bengineer91/Preamp/layout/back.PNG

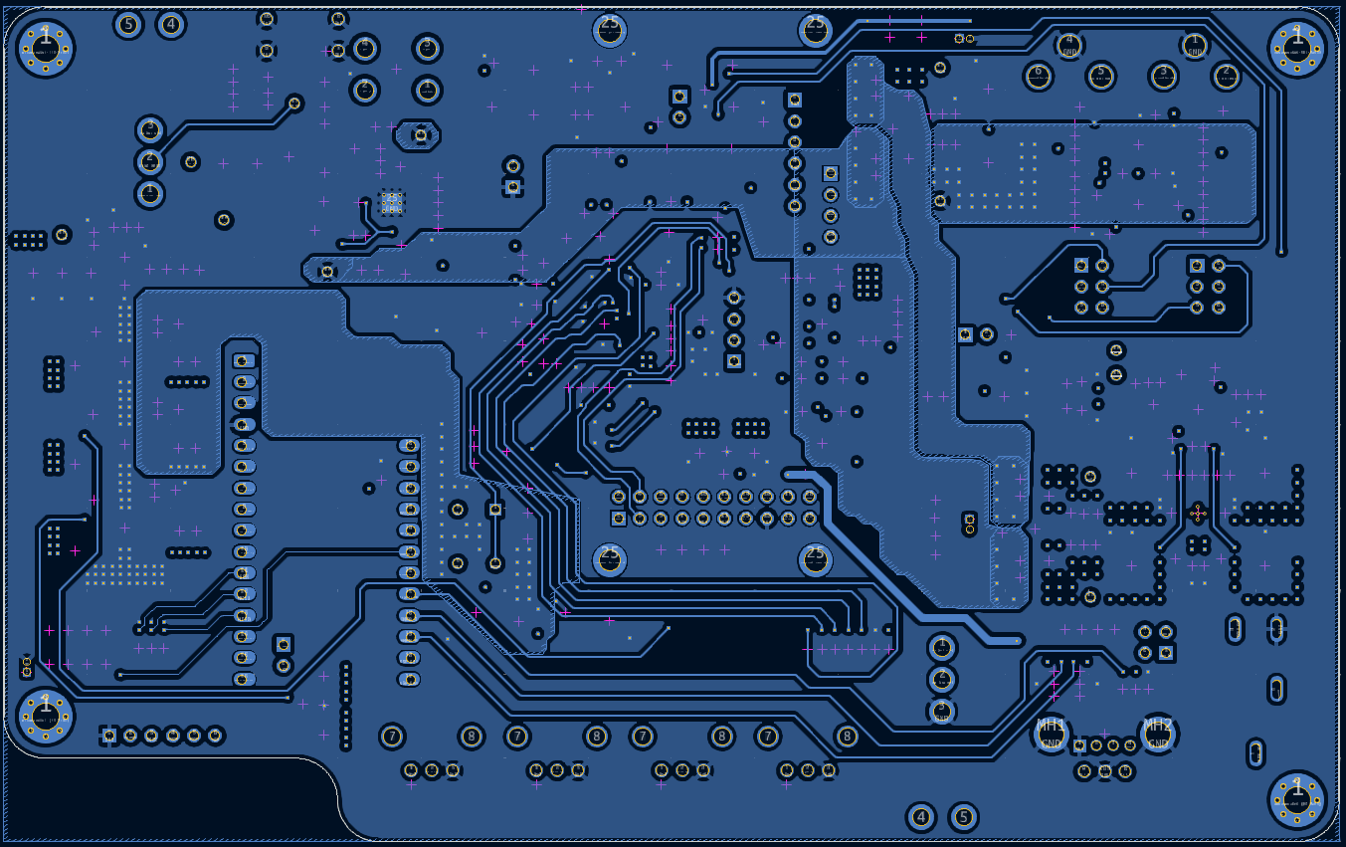
layout/back.PNG
