bengineer91/Preamp/layout/front.PNG

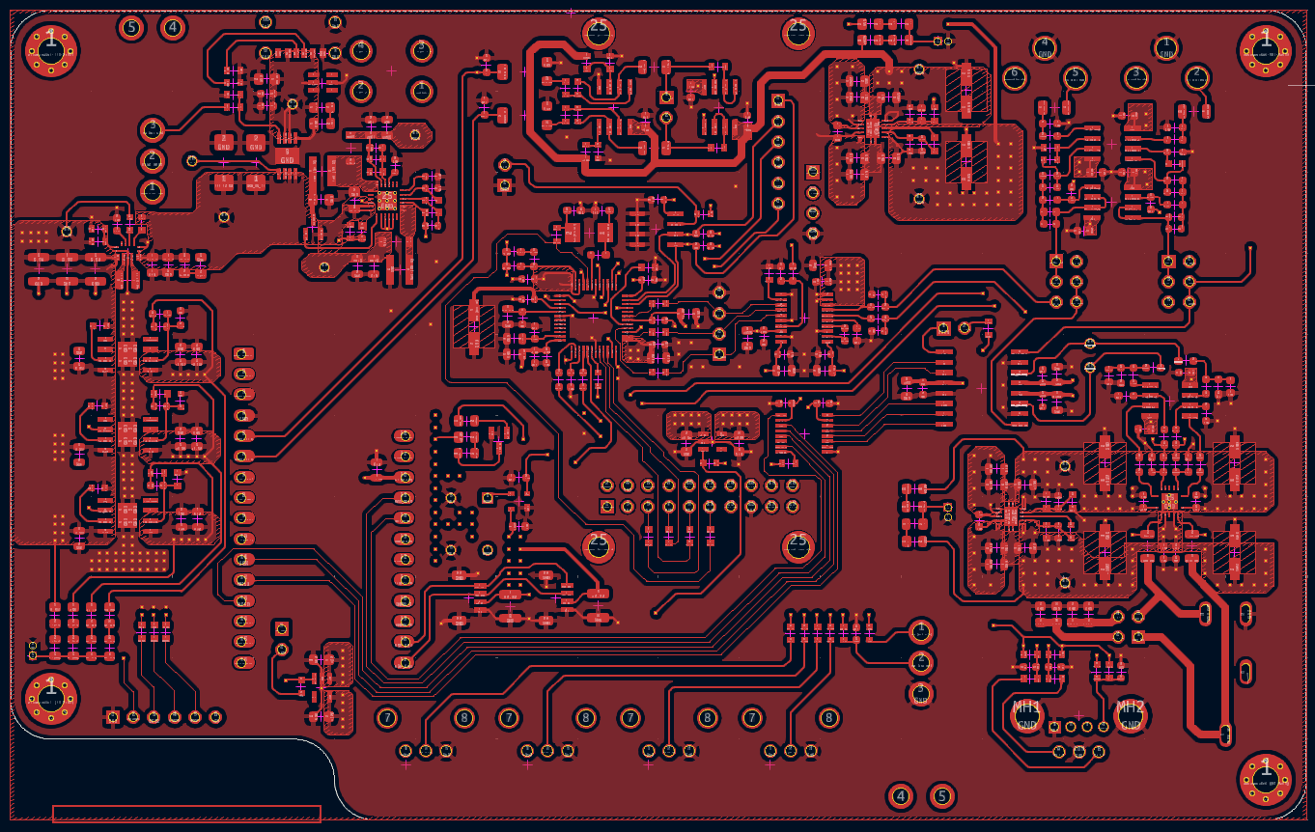
layout/front.PNG
