bengineer91/Preamp/layout/front_w_silk.PNG

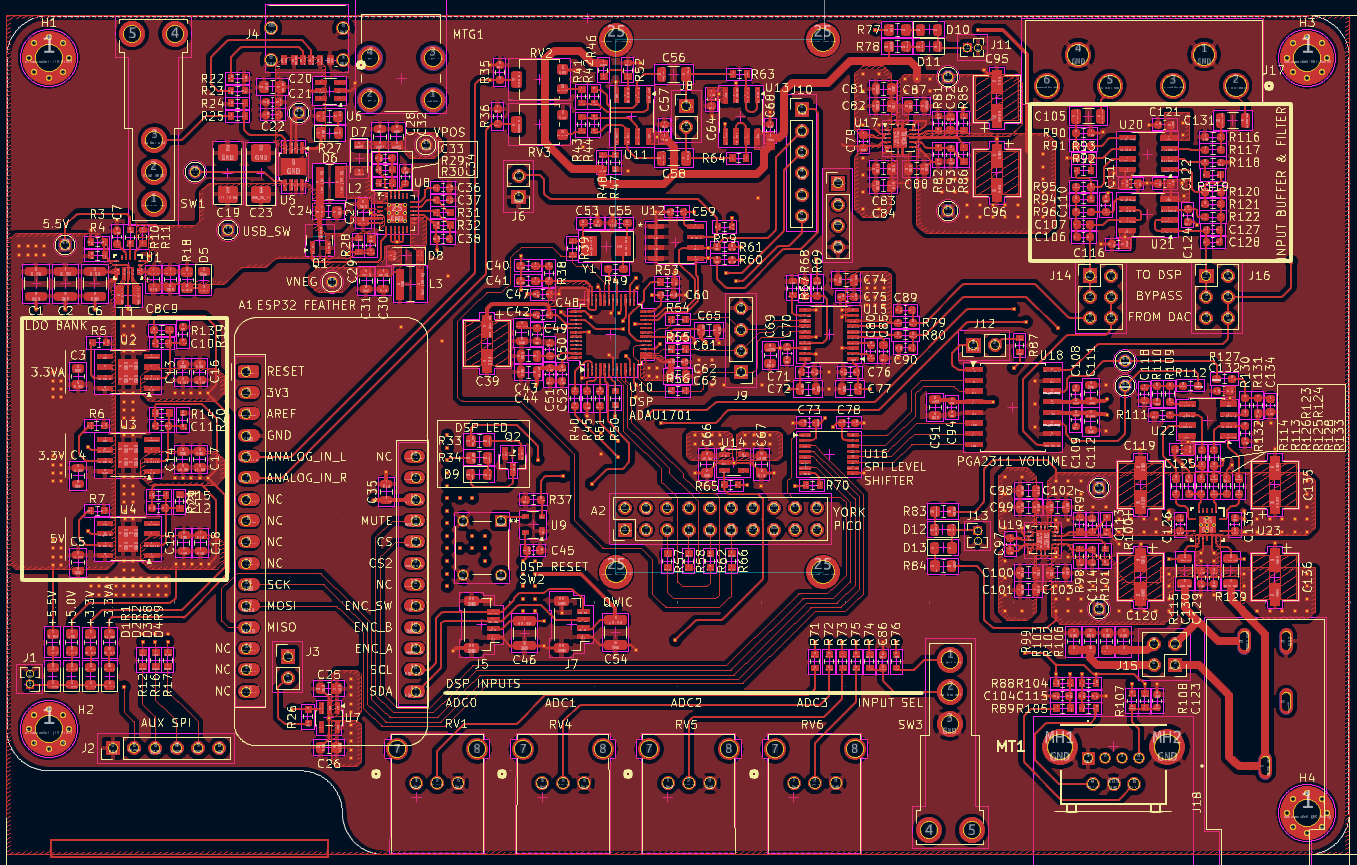
layout/front_w_silk.PNG
