bengineer91/Preamp/layout/in1_gnd.PNG

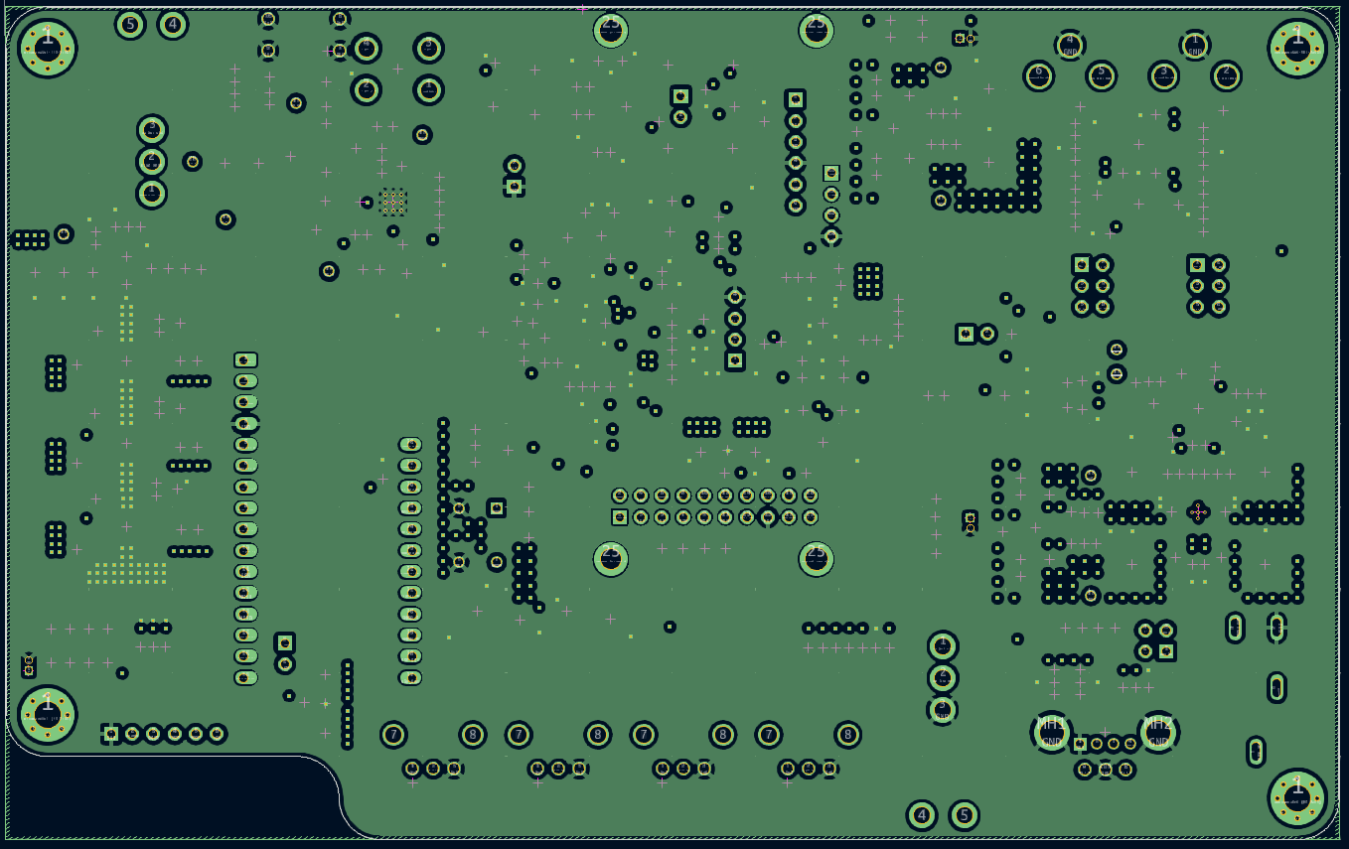
layout/in1_gnd.PNG
