bengineer91/Preamp/layout/in2_pwr.PNG

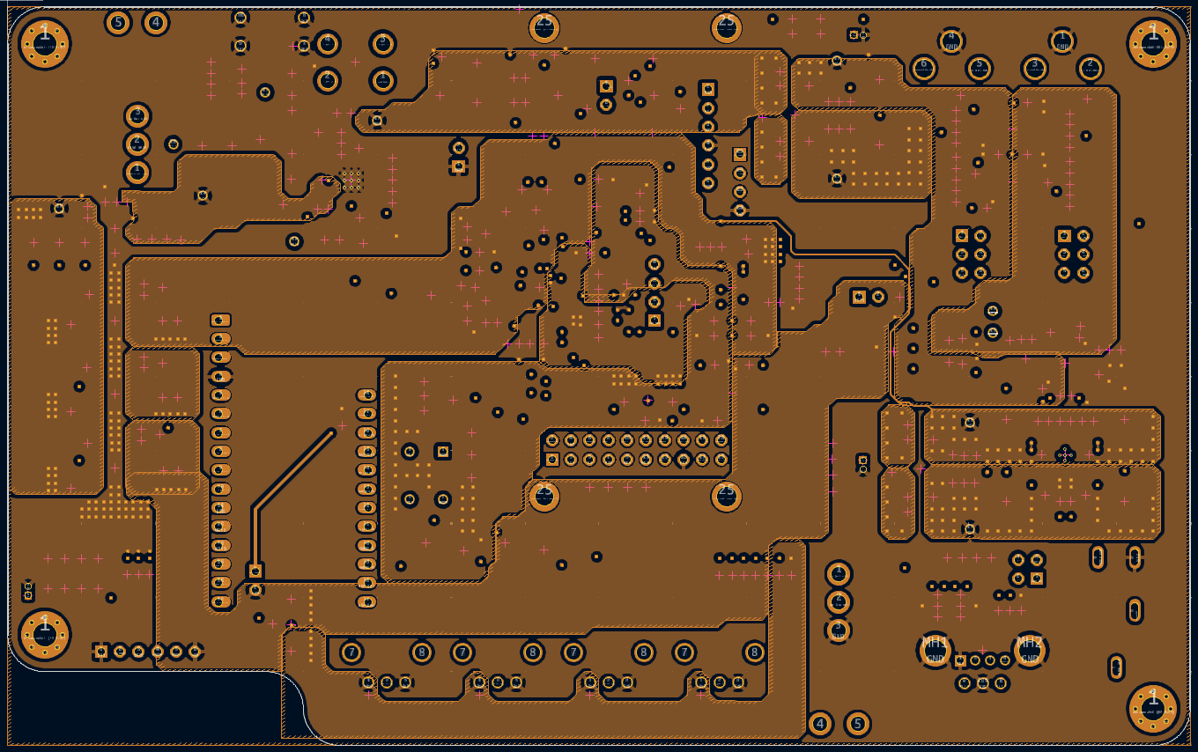
layout/in2_pwr.PNG
