bengineer91/Preamp/schematic/sheet2.png

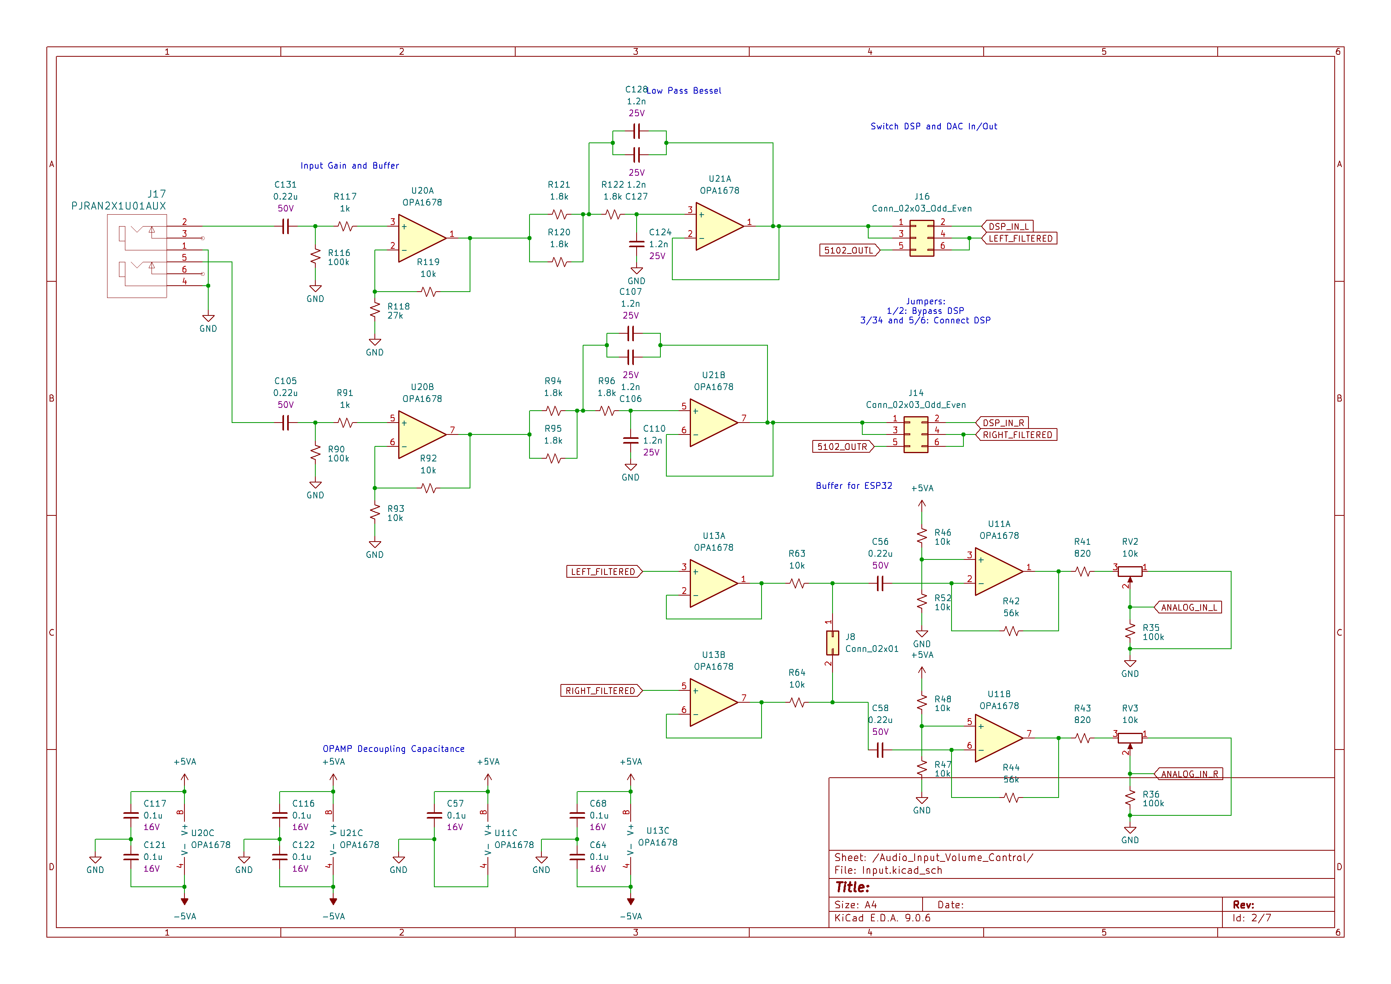
schematic/sheet2.png
