bengineer91/Preamp/schematic/sheet6.png

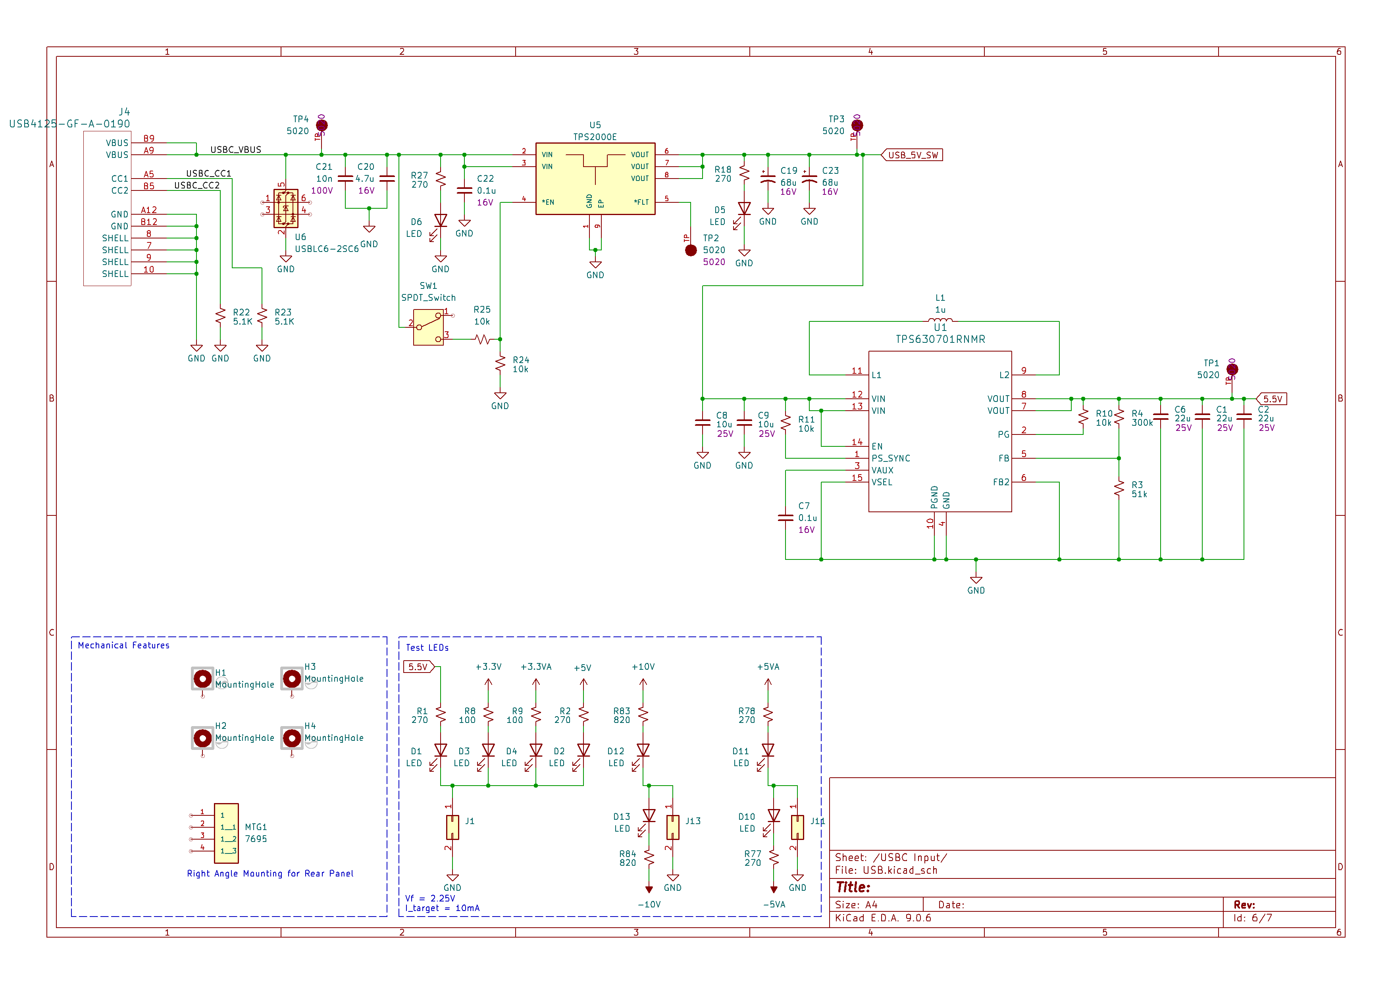
schematic/sheet6.png
