bengineer91/Preamp/schematic/sheet7.png

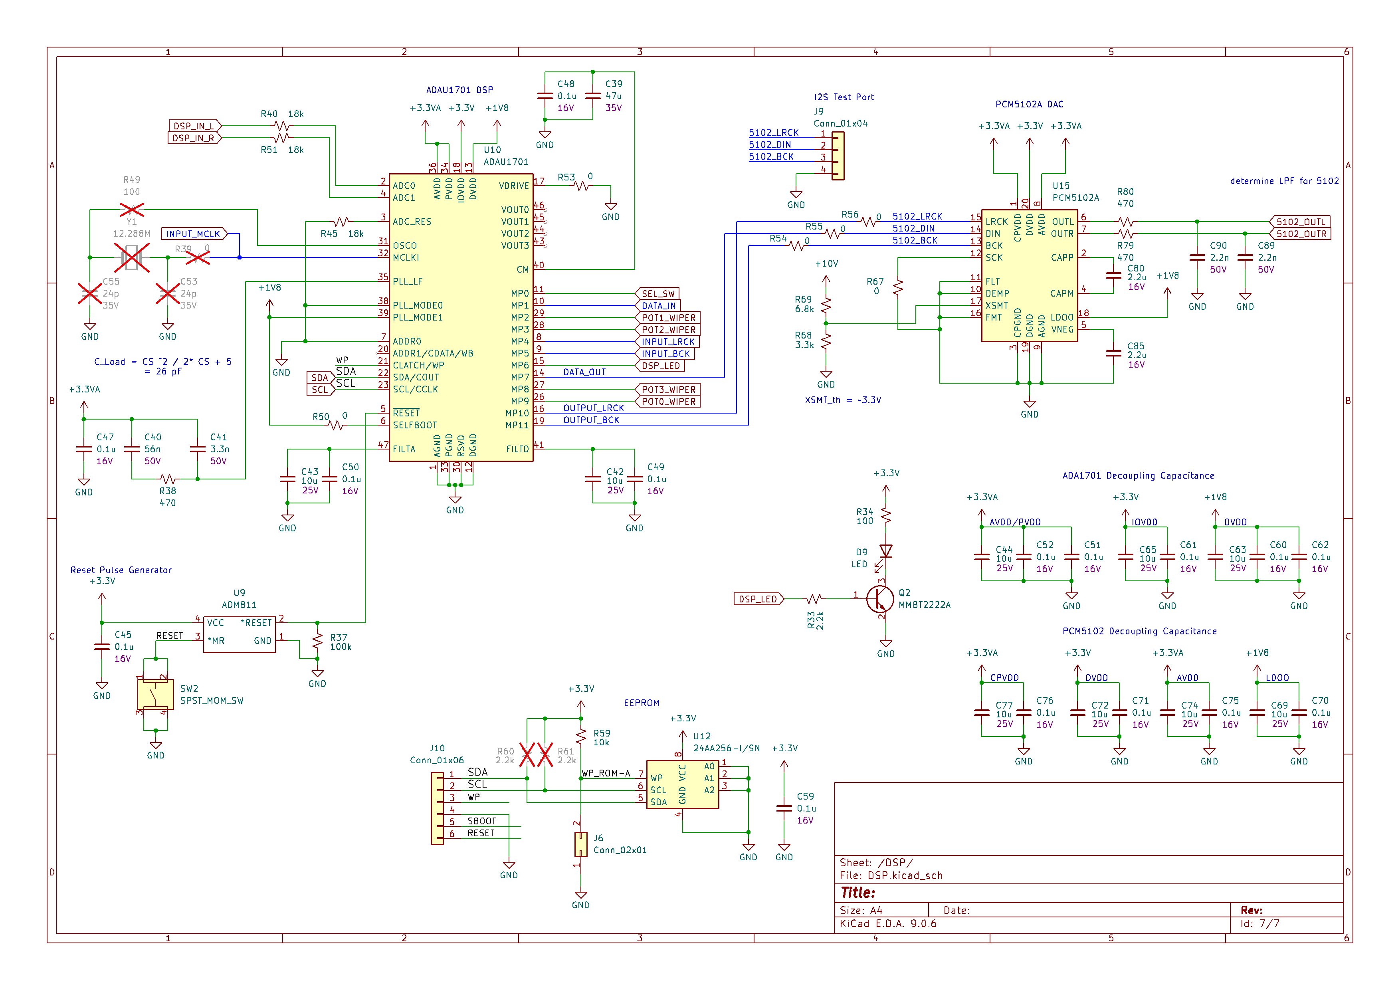
schematic/sheet7.png
