bengineer91/Preamp/kicad/DSP.kicad_sch

## KiCad design kicad/DSP.kicad_sch (2026-02-03)

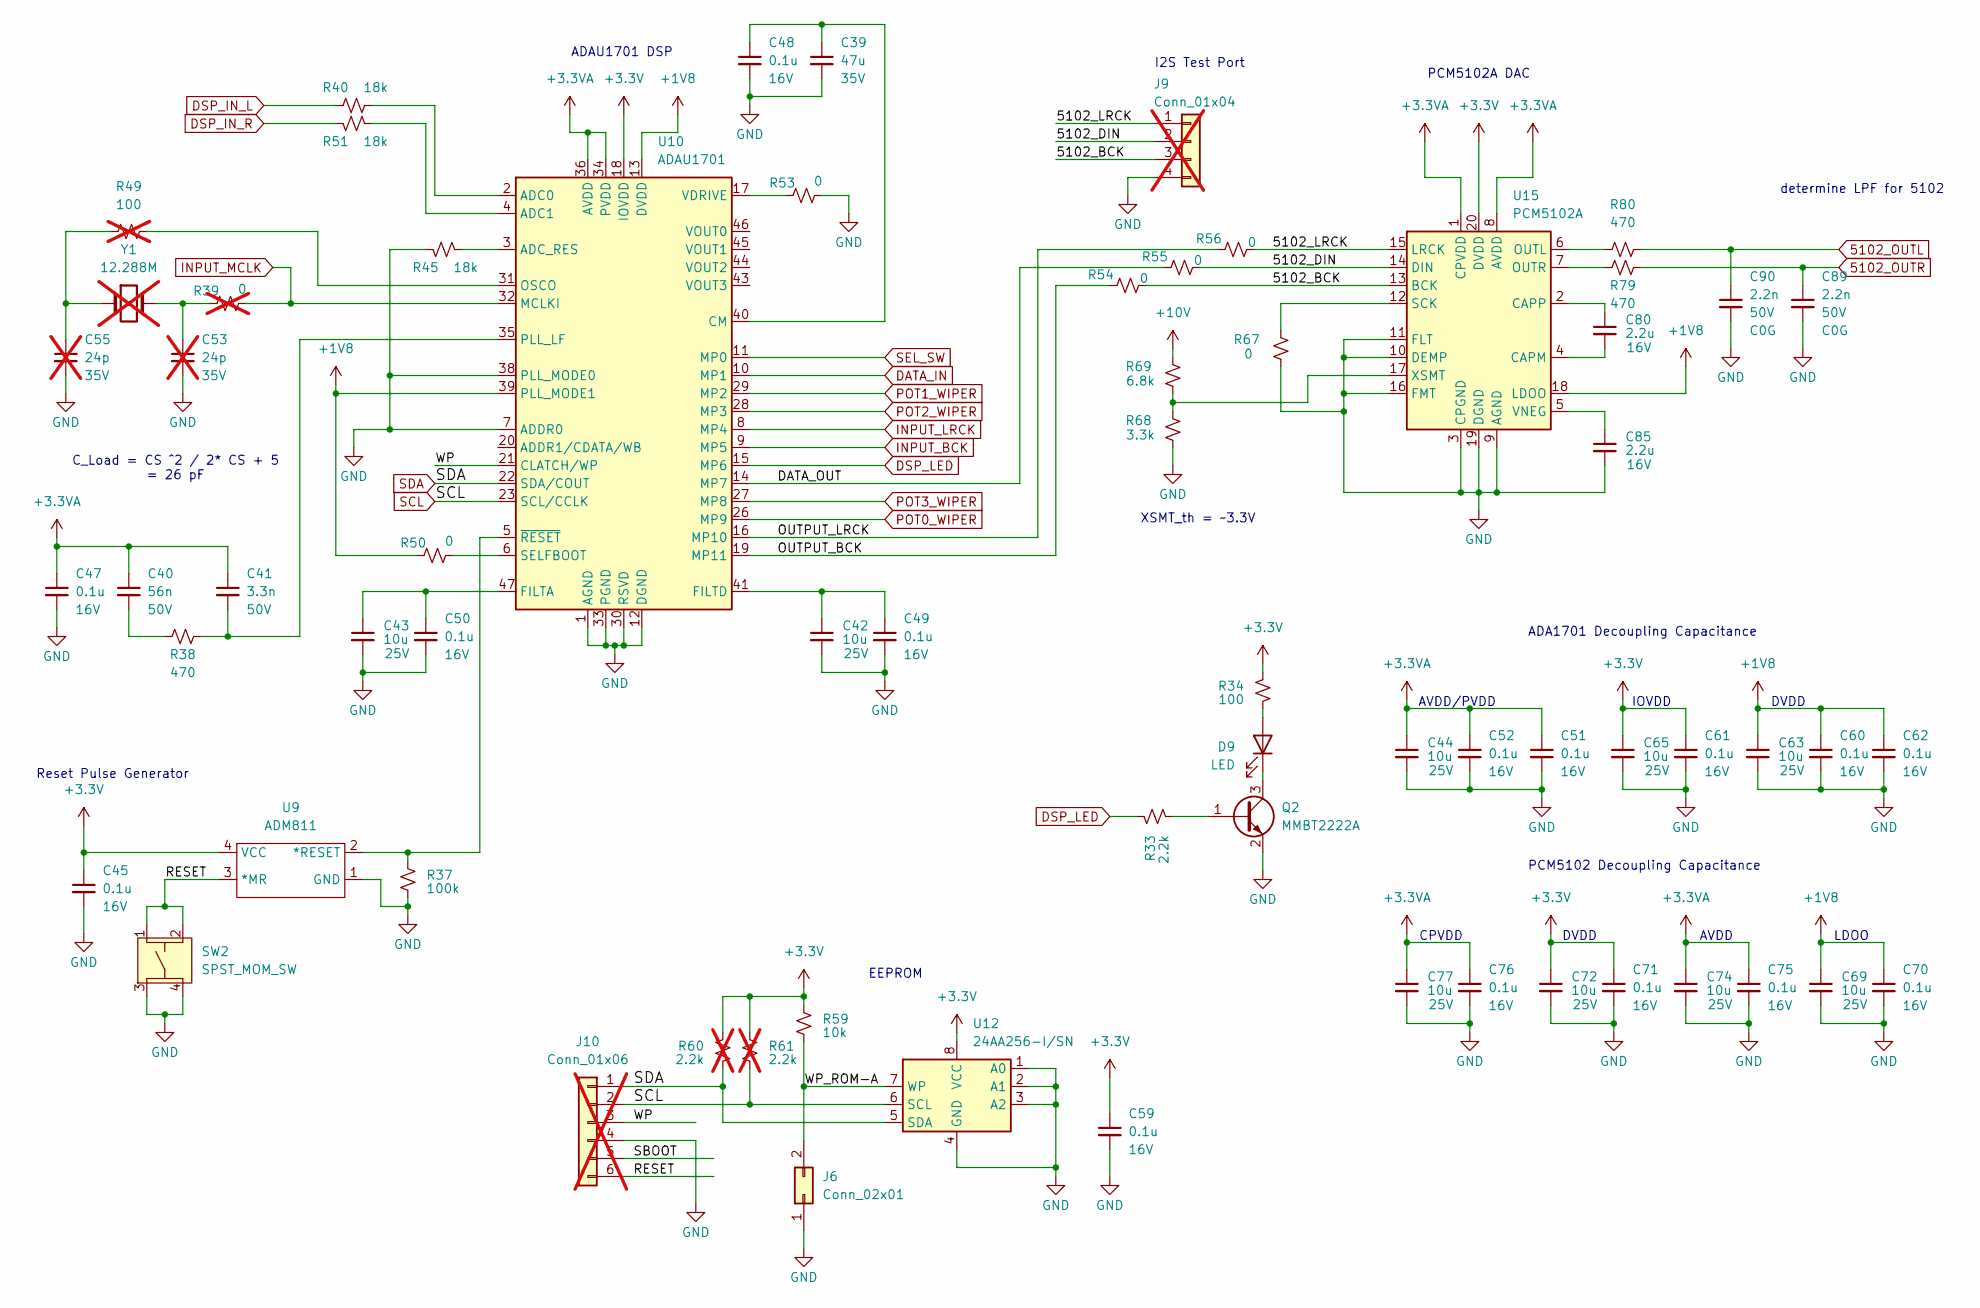
[picture p24: schematic DSP.kicad_sch]

Parts:
C39: 47u; CAP_UCD_5X5P8_NCH; Voltage 35V; Part Number UCM1V470MCL1GS
C40: 56n; C_0603_1608Metric_Pad1.08x0.95mm_HandSolder; Voltage 50V; Part Number GCM188R71H563KA57D
C41: 3.3n; C_0603_1608Metric_Pad1.08x0.95mm_HandSolder; Voltage 50V; Part Number GRM1885C1H332JA01D
C42, C43, C44, C63, C65, C69, C72, C74, C77: 10u; C_0805_2012Metric; Voltage 25V; Part Number GRM21BZ71E106KE15L
C45, C47, C48, C49, C50, C51, C52, C59, C60, C61, C62, C70, C71, C75, C76: 0.1u; C_0603_1608Metric; Voltage 16V; Part Number GCJ188R71C104KA01D
C53, C55: 24p; C_0603_1608Metric_Pad1.08x0.95mm_HandSolder; Voltage 35V; not fitted
C80, C85: 2.2u; C_0603_1608Metric; Voltage 16V; Part Number GRM188Z71E225ME43D
C89, C90: 2.2n; C_0603_1608Metric; Voltage 50V; Part Number GRM1885C1H222JA01D
D9: LED; LED_0805_2012Metric_Pad1.15x1.40mm_HandSolder; Part Number APT2012PGW
J6: Conn_02x01; PinHeader_1x02_P2.54mm_Vertical
J9: Conn_01x04; PinHeader_1x04_P2.54mm_Vertical; not fitted
J10: Conn_01x06; PinHeader_1x06_P2.54mm_Vertical; not fitted
Q2: MMBT2222A; SOT-23; Part Number MMBT2222A
R33: 2.2k; R_0805_2012Metric_Pad1.20x1.40mm_HandSolder; Part Number CRCW08052K20FKEA
R34: 100; R_0805_2012Metric_HandSolder; Part Number CRCW0805150RFKEA
R37: 100k; R_0603_1608Metric; Part Number CRCW0603100KFKEA
R38, R79, R80: 470; R_0603_1608Metric; Part Number CRCW0603470RFKEA
R39: 0; R_0603_1608Metric; Part Number CRCW06030000Z0EA; not fitted
R40, R45, R51: 18k; R_0603_1608Metric; Part Number CRCW060318K0FKEA
R49: 100; R_0603_1608Metric_Pad0.98x0.95mm_HandSolder; Part Number CRCW0805100RFKEA; not fitted
R50, R53, R54, R55, R56, R67: 0; R_0603_1608Metric; Part Number CRCW06030000Z0EA
R59: 10k; R_0603_1608Metric; Part Number CRCW060310K0FKEA
R60, R61: 2.2k; R_0603_1608Metric_Pad0.98x0.95mm_HandSolder; Part Number CRCW06032K20FKEA; not fitted
R68: 3.3k; R_0603_1608Metric_Pad0.98x0.95mm_HandSolder
R69: 6.8k; R_0603_1608Metric
SW2: SPST_MOM_SW; SW4_1825910-B_TEC
U9: ADM811; SOT-143; Part Number ADM811-3TARTZ-RL7
U10: ADAU1701; LQFP-48_7x7mm_P0.5mm; Manufacturer_Part_Number ADAU1701JSTZ-RL
U12: 24AA256-I/SN; SOIC8-N_MC_MCH; Part Number 24AA256-I/SN
U15: PCM5102A; TSSOP-20_4.4x6.5mm_P0.65mm; Manufacturer_Part_Number PCM5102APWR
Y1: 12.288M; Crystal_SMD_Abracon_ABM3-2Pin_5.0x3.2mm; not fitted

Connections:
5102_BCK: J9.3, R54.2, U15.13 (BCK)
5102_DIN: J9.2, R55.2, U15.14 (DIN)
5102_LRCK: J9.1, R56.2, U15.15 (LRCK)
5102_OUTL: C90.1, R80.2
5102_OUTR: C89.1, R79.2
+1V8: C60.1, C62.1, C63.1, C69.1, C70.1, R50.1, U10.13 (DVDD), U10.24 (DVDD), U10.39 (PLL_MODE1), U15.18 (LDOO)
+3.3V: C45.1, C59.1, C61.1, C65.1, C71.1, C72.1, R34.1, R59.1, R60.1, R61.1, U9.4 (VCC), U10.18 (IOVDD), U12.8 (VCC), U15.20 (DVDD)
+3.3VA: C40.1, C41.1, C44.1, C47.1, C51.1, C52.1, C74.1, C75.1, C76.1, C77.1, U10.34 (PVDD), U10.36 (AVDD), U10.48 (AVDD), U15.1 (CPVDD), U15.8 (AVDD)
+10V: R69.2
DATA_IN: U10.10 (MP1)
DATA_OUT: R55.1, U10.14 (MP7)
DSP_IN_L: R40.1
DSP_IN_R: R51.1
DSP_LED: R33.1, U10.15 (MP6)
GND: C39.2, C42.2, C43.2, C44.2, C45.2, C47.2, C48.2, C49.2, C50.2, C51.2, C52.2, C53.2, C55.2, C59.2, C60.2, C61.2, C62.2, C63.2, C65.2, C69.2, C70.2, C71.2, C72.2, C74.2, C75.2, C76.2, C77.2, C85.2, C89.2, C90.2, J6.1, J9.4, J10.4, Q2.2 (E), R37.1, R45.1, R53.2, R67.1, R68.1, SW2.3 (2), SW2.4 (2), U9.1 (GND), U10.1 (AGND), U10.7 (ADDR0), U10.12 (DGND), U10.25 (DGND), U10.30 (RSVD), U10.33 (PGND), U10.37 (AGND), U10.38 (PLL_MODE0), U10.42 (AGND), U12.1 (A0), U12.2 (A1), U12.3 (A2), U12.4 (GND), U15.3 (CPGND), U15.9 (AGND), U15.10 (DEMP), U15.11 (FLT), U15.16 (FMT), U15.19 (DGND)
INPUT_BCK: U10.9 (MP5)
INPUT_LRCK: U10.8 (MP4)
INPUT_MCLK: R39.2, U10.32 (MCLKI)
unnamed: C39.1, C48.1, U10.40 (CM)
unnamed: C40.2, R38.1
unnamed: C41.2, R38.2, U10.35 (PLL_LF)
unnamed: C42.1, C49.1, U10.41 (FILTD)
unnamed: C43.1, C50.1, U10.47 (FILTA)
unnamed: C53.1, R39.1, Y1.2
unnamed: C55.1, R49.1, Y1.1
unnamed: C80.1, U15.2 (CAPP)
unnamed: C80.2, U15.4 (CAPM)
unnamed: C85.1, U15.5 (VNEG)
unnamed: D9.1 (K), Q2.3 (C)
unnamed: D9.2 (A), R34.2
unnamed: Q2.1 (B), R33.2
unnamed: R37.2, U9.2 (*RESET), U10.5 (~RESET)
unnamed: R40.2, U10.2 (ADC0)
unnamed: R45.2, U10.3 (ADC_RES)
unnamed: R49.2, U10.31 (OSCO)
unnamed: R50.2, U10.6 (SELFBOOT)
unnamed: R51.2, U10.4 (ADC1)
unnamed: R53.1, U10.17 (VDRIVE)
unnamed: R67.2, U15.12 (SCK)
unnamed: R68.2, R69.1, U15.17 (XSMT)
unnamed: R79.1, U15.7 (OUTR)
unnamed: R80.1, U15.6 (OUTL)
OUTPUT_BCK: R54.1, U10.19 (MP11)
OUTPUT_LRCK: R56.1, U10.16 (MP10)
POT0_WIPER: U10.26 (MP9)
POT1_WIPER: U10.29 (MP2)
POT2_WIPER: U10.28 (MP3)
POT3_WIPER: U10.27 (MP8)
RESET: J10.6, SW2.1, SW2.2 (1), U9.3 (*MR)
SBOOT: J10.5
SCL: J10.2, R61.2, U10.23 (SCL/CCLK), U12.6 (SCL)
SDA: J10.1, R60.2, U10.22 (SDA/COUT), U12.5 (SDA)
SEL_SW: U10.11 (MP0)
WP: J10.3, U10.21 (CLATCH/WP)
WP_ROM-A: J6.2, R59.2, U12.7 (WP)

Notes on the sheet:
LDOO
ADAU1701 DSP
ADA1701 Decoupling Capacitance
XSMT_th = ~3.3V
PCM5102A DAC
DVDD
IOVDD
Reset Pulse Generator
AVDD/PVDD
PCM5102 Decoupling Capacitance
C_Load = CS ^2 / 2* CS + 5 = 26 pF
EEPROM
AVDD
determine LPF for 5102
I2S Test Port
CPVDD
