bengineer91/Preamp/kicad/Digital.kicad_sch

## KiCad design kicad/Digital.kicad_sch (2026-02-03)

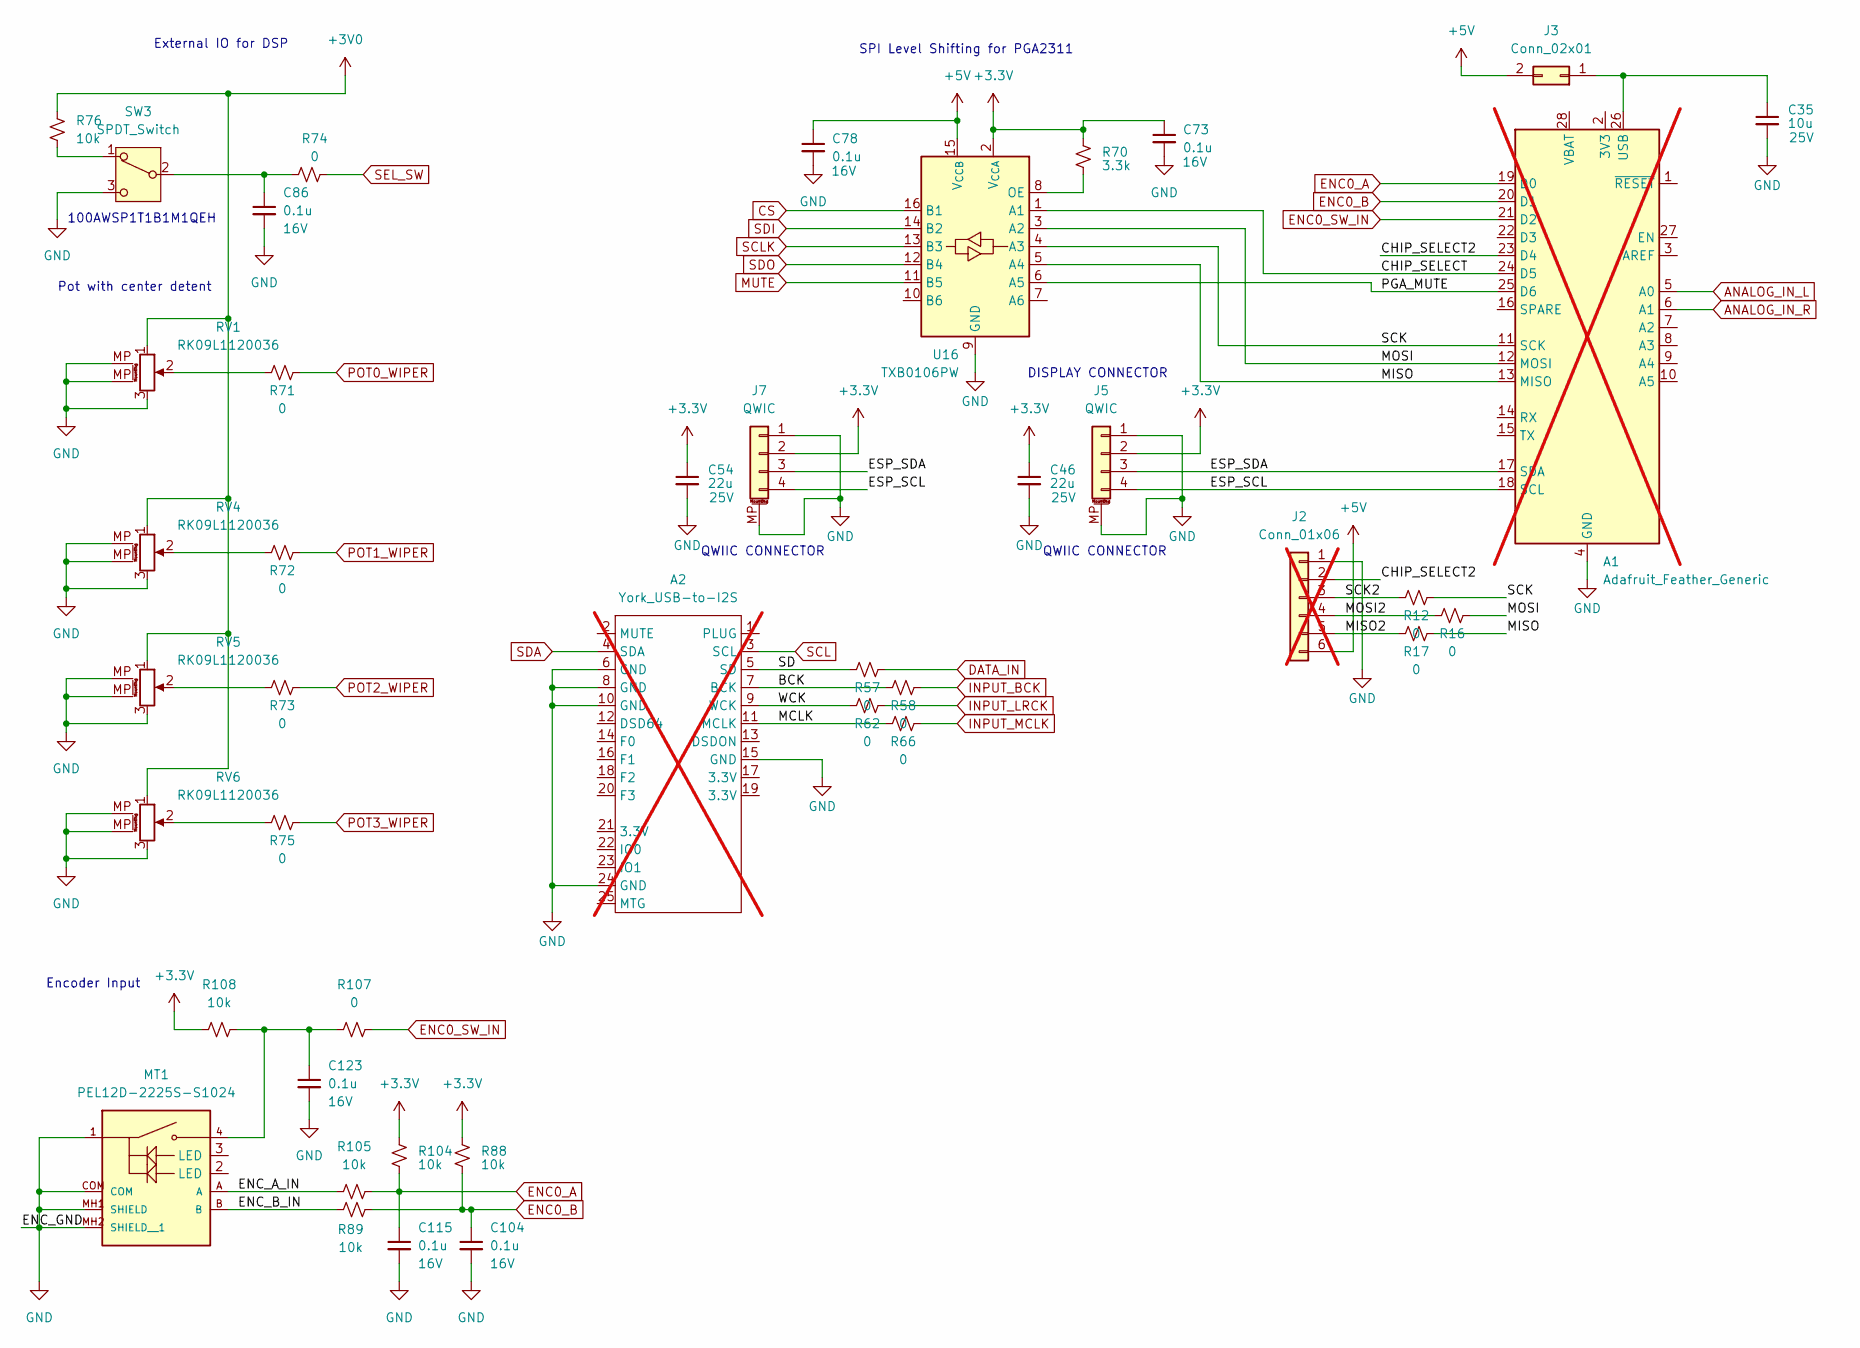
[picture p25: schematic Digital.kicad_sch]

Parts:
A1: Adafruit_Feather_Generic; Adafruit_Feather2; not fitted
A2: York_USB-to-I2S; York_Pico_USB-to-I2S; not fitted
C35: 10u; C_0805_2012Metric; Voltage 25V; Part Number GRM21BZ71E106KE15L
C46, C54: 22u; C_1210_3225Metric; Voltage 25V; Part Number GRM32ER71E226ME15L
C73, C78, C86, C104, C115, C123: 0.1u; C_0603_1608Metric; Voltage 16V; Part Number GCJ188R71C104KA01D
J2: Conn_01x06; PinHeader_1x06_P2.54mm_Vertical; not fitted
J3: Conn_02x01; PinHeader_1x02_P2.54mm_Vertical
J5, J7: QWIC; JST_SH_BM04B-SRSS-TB_1x04-1MP_P1.00mm_Vertical
MT1: PEL12D-2225S-S1024; PEL12D2225SS1024; PARTREV Rev. 09/19
R12, R16, R17, R57, R58, R62, R66, R71, R72, R73, R74, R75, R107: 0; R_0603_1608Metric; Part Number CRCW06030000Z0EA
R70: 3.3k; R_0603_1608Metric; Part Number CRCW08053K30FKEA
R76, R88, R89, R104, R105, R108: 10k; R_0603_1608Metric; Part Number CRCW060310K0FKEA
RV1, RV4, RV5, RV6: RK09L1120036
SW3: SPDT_Switch; 100AWSP1T2B4M7RE
U16: TXB0106PW; TSSOP-16_4.4x5mm_P0.65mm; Part Number TXB0106PW

Connections:
+3.3V: C46.1, C54.1, C73.1, J5.2, J7.2, R70.2, R88.1, R104.1, R108.1, U16.2 (V_{CCA})
+3V0: R76.2, RV1.1, RV4.1, RV5.1, RV6.1
+5V: C78.1, J2.6, J3.2, U16.15 (V_{CCB})
ANALOG_IN_L: A1.5 (A0)
ANALOG_IN_R: A1.6 (A1)
BCK: A2.7 (BCK), R58.1
CHIP_SELECT: A1.24 (D5), U16.1 (A1)
CHIP_SELECT2: A1.23 (D4), J2.2
CS: U16.16 (B1)
DATA_IN: R57.2
ENC0_A: A1.19 (D0), C115.1, R104.2, R105.2
ENC0_B: A1.20 (D1), C104.1, R88.2, R89.2
ENC0_SW_IN: A1.21 (D2), R107.2
ENC_A_IN: MT1.A, R105.1
ENC_B_IN: MT1.B, R89.1
ESP_SCL: A1.18 (SCL), J5.4, J7.4
ESP_SDA: A1.17 (SDA), J5.3, J7.3
GND: A1.4 (GND), A2.6 (GND), A2.8 (GND), A2.10 (GND), A2.15 (GND), A2.24 (GND), C35.2, C46.2, C54.2, C73.2, C78.2, C86.2, C104.2, C115.2, C123.2, J2.1, J5.1, J5.MP (MountPin), J7.1, J7.MP (MountPin), MT1.1, MT1.COM, MT1.MH1 (SHIELD), MT1.MH2 (SHIELD__1), RV1.3, RV1.MP (MountPin), RV4.3, RV4.MP (MountPin), RV5.3, RV5.MP (MountPin), RV6.3, RV6.MP (MountPin), SW3.3 (ON), U16.9 (GND)
INPUT_BCK: R58.2
INPUT_LRCK: R62.2
INPUT_MCLK: R66.2
MCLK: A2.11 (MCLK), R66.1
MISO: A1.13 (MISO), R17.2, U16.5 (A4)
MISO2: J2.5, R17.1
MOSI: A1.12 (MOSI), R16.2, U16.3 (A2)
MOSI2: J2.4, R16.1
MUTE: U16.11 (B5)
unnamed: A1.26 (USB), C35.1, J3.1
unnamed: C86.1, R74.1, SW3.2 (COM)
unnamed: C123.1, MT1.4, R107.1, R108.2
unnamed: R70.1, U16.8 (OE)
unnamed: R71.1, RV1.2
unnamed: R72.1, RV4.2
unnamed: R73.1, RV5.2
unnamed: R75.1, RV6.2
unnamed: R76.1, SW3.1 (ON)
PGA_MUTE: A1.25 (D6), U16.6 (A5)
POT0_WIPER: R71.2
POT1_WIPER: R72.2
POT2_WIPER: R73.2
POT3_WIPER: R75.2
SCK: A1.11 (SCK), R12.2, U16.4 (A3)
SCK2: J2.3, R12.1
SCL: A2.3 (SCL)
SCLK: U16.13 (B3)
SD: A2.5 (SD), R57.1
SDA: A2.4 (SDA)
SDI: U16.14 (B2)
SDO: U16.12 (B4)
SEL_SW: R74.2
WCK: A2.9 (WCK), R62.1

Notes on the sheet:
QWIIC CONNECTOR
Pot with center detent
100AWSP1T1B1M1QEH
Encoder Input
External IO for DSP
DISPLAY CONNECTOR
SPI Level Shifting for PGA2311
