bengineer91/Preamp/kicad/Input.kicad_sch

## KiCad design kicad/Input.kicad_sch (2026-02-03)

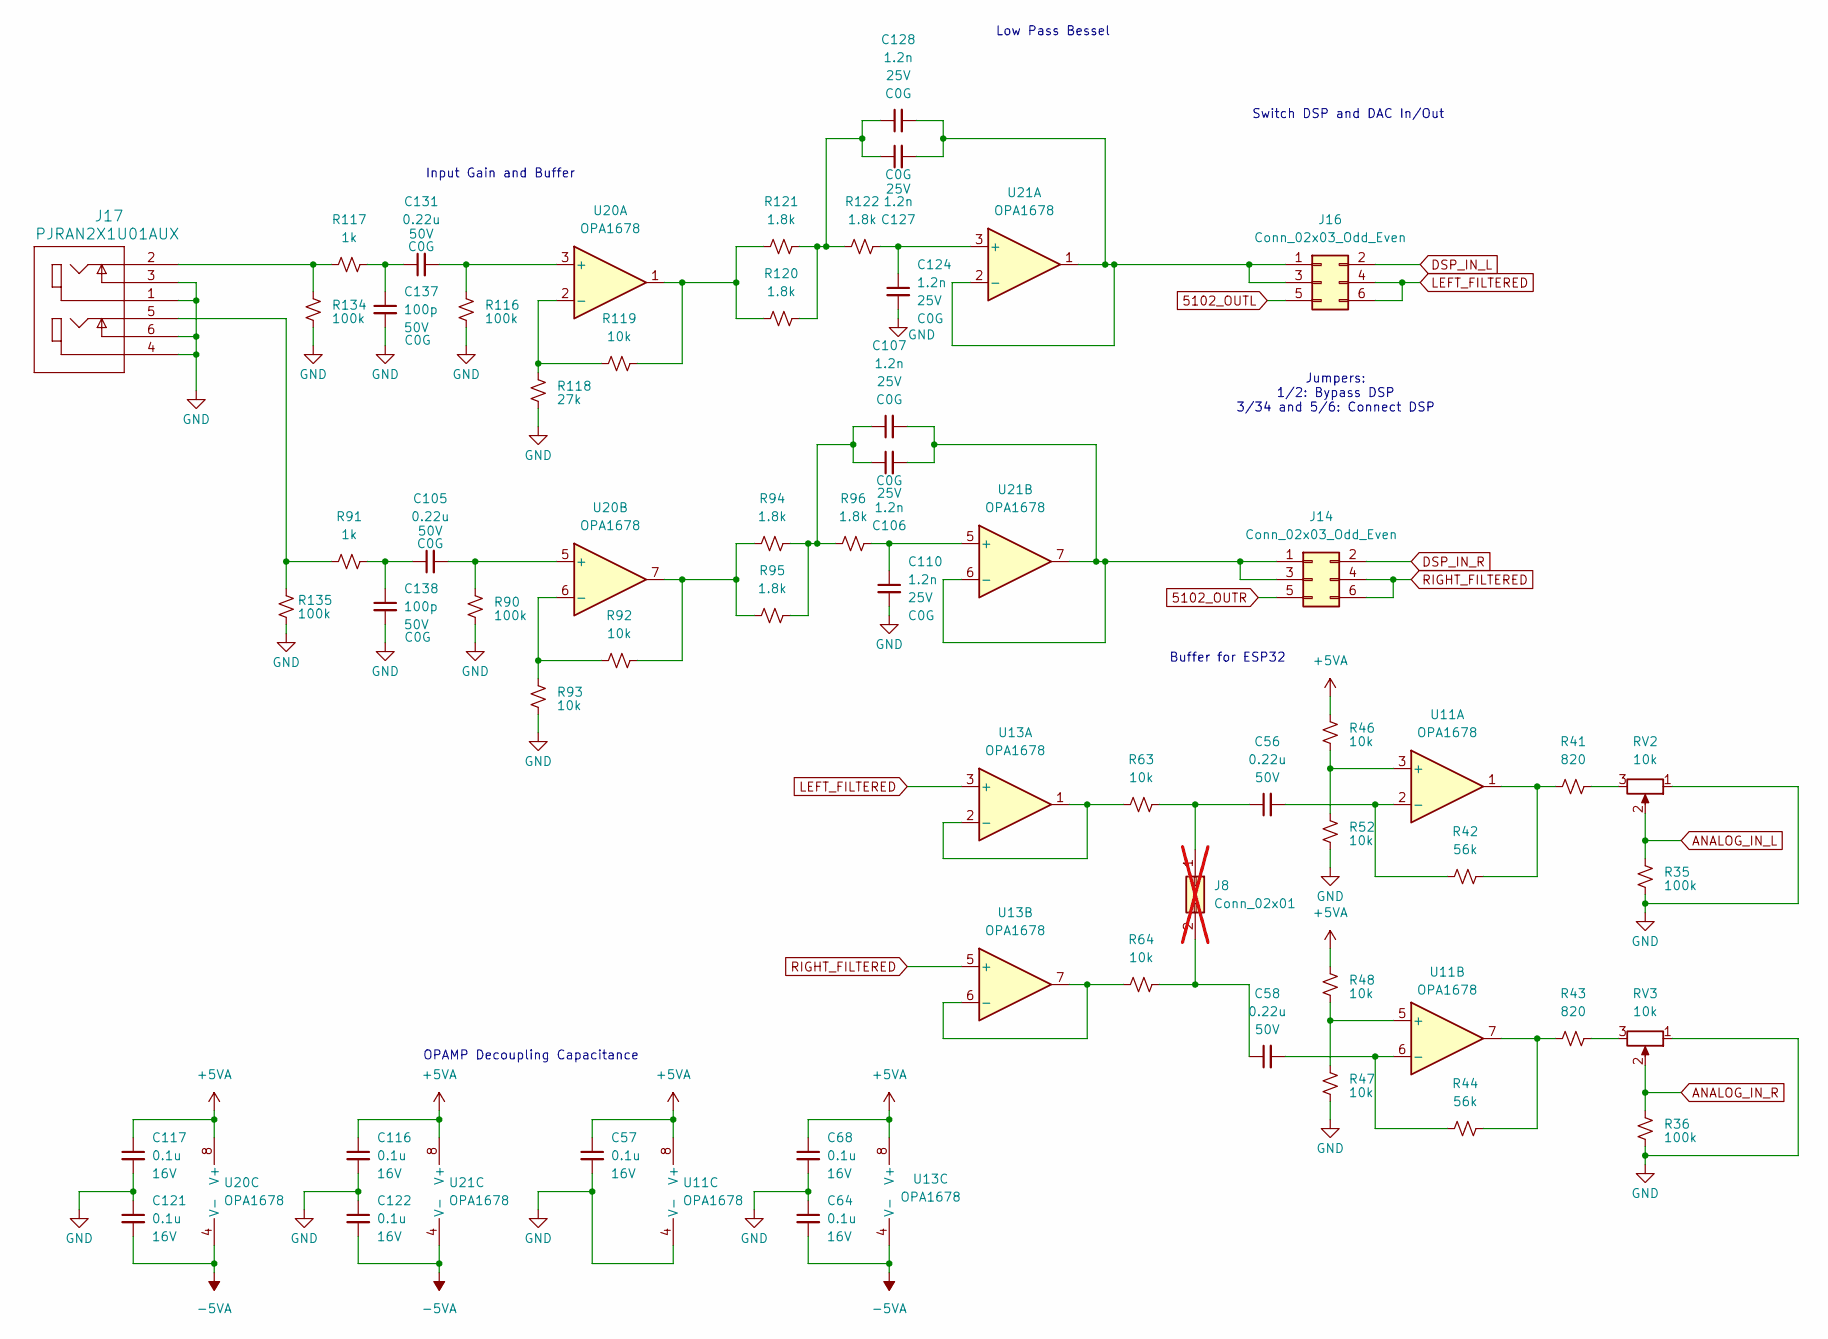
[picture p26: schematic Input.kicad_sch]

Parts:
C56, C58, C105, C131: 0.22u; C_1206_3216Metric; Voltage 50V; Part Number GRM31C5C1H224JE02L
C57, C64, C68, C116, C117, C121, C122: 0.1u; C_0603_1608Metric; Voltage 16V; Part Number GCJ188R71C104KA01D
C106, C107, C110, C124, C127, C128: 1.2n; C_0603_1608Metric; Voltage 25V; Part Number GRM1885C1E122JA01D
C137, C138: 100p; C_0603_1608Metric; Voltage 50V; Part Number GRM1885C1H101JA01D
J8: Conn_02x01; PinHeader_1x02_P2.54mm_Vertical; not fitted
J14, J16: Conn_02x03_Odd_Even; PinHeader_2x03_P2.54mm_Vertical
J17: PJRAN2X1U01AUX; CONN6_984x394_SWC_BS; Part Number PJRAN2X1U01AUX
R35, R36, R90, R116, R134, R135: 100k; R_0603_1608Metric; Part Number CRCW0603100KFKEA
R41, R43: 820; R_0603_1608Metric; Part Number CRCW0805820RFKEA
R42, R44: 56k; R_0603_1608Metric; Part Number CRCW060356K0FKEA
R46, R47, R48, R52, R63, R64, R92, R93, R119: 10k; R_0603_1608Metric; Part Number CRCW060310K0FKEA
R91, R117: 1k; R_0603_1608Metric; Part Number CRCW06031K00FKEA
R94, R95, R96, R120, R121, R122: 1.8k; R_0603_1608Metric; Part Number CRCW06031K80FKEA
R118: 27k; R_0603_1608Metric; Part Number CRCW060327K0FKEA
RV2, RV3: 10k; Potentiometer_Bourns_3314G_Vertical
U11, U13, U20, U21: OPA1678; SOIC-8_3.9x4.9mm_P1.27mm; Part Number OPA1678IDR

Connections:
5102_OUTL: J16.5
5102_OUTR: J14.5
+5VA: C57.1, C68.1, C116.1, C117.1, R46.2, R48.2, U11.8 (V+), U13.8 (V+), U20.8 (V+), U21.8 (V+)
-5VA: C64.2, C121.2, C122.2, U13.4 (V-), U20.4 (V-), U21.4 (V-)
ANALOG_IN_L: R35.2, RV2.2
ANALOG_IN_R: R36.2, RV3.2
DSP_IN_L: J16.2
DSP_IN_R: J14.2
GND: C57.2, C64.1, C68.2, C110.2, C116.2, C117.2, C121.1, C122.1, C124.2, C137.2, C138.2, J17.1, J17.3, J17.4, J17.6, R35.1, R36.1, R47.1, R52.1, R90.1, R93.1, R116.1, R118.1, R134.1, R135.1, RV2.1, RV3.1, U11.4 (V-)
LEFT_FILTERED: J16.4, J16.6, U13.3 (+)
unnamed: C56.1, J8.1, R63.1
unnamed: C56.2, R42.2, U11.2 (-)
unnamed: C58.1, J8.2, R64.1
unnamed: C58.2, R44.2, U11.6 (-)
unnamed: C105.1, C138.1, R91.1
unnamed: C105.2, R90.2, U20.5 (+)
unnamed: C106.1, C107.1, R94.1, R95.1, R96.2
unnamed: C106.2, C107.2, J14.1, J14.3, U21.6 (-), U21.7
unnamed: C110.1, R96.1, U21.5 (+)
unnamed: C124.1, R122.1, U21.3 (+)
unnamed: C127.1, C128.1, R120.1, R121.1, R122.2
unnamed: C127.2, C128.2, J16.1, J16.3, U21.1, U21.2 (-)
unnamed: C131.1, C137.1, R117.1
unnamed: C131.2, R116.2, U20.3 (+)
unnamed: J17.2, R117.2, R134.2
unnamed: J17.5, R91.2, R135.2
unnamed: R41.1, RV2.3
unnamed: R41.2, R42.1, U11.1
unnamed: R43.1, RV3.3
unnamed: R43.2, R44.1, U11.7
unnamed: R46.1, R52.2, U11.3 (+)
unnamed: R47.2, R48.1, U11.5 (+)
unnamed: R63.2, U13.1, U13.2 (-)
unnamed: R64.2, U13.6 (-), U13.7
unnamed: R92.1, R94.2, R95.2, U20.7
unnamed: R92.2, R93.2, U20.6 (-)
unnamed: R118.2, R119.2, U20.2 (-)
unnamed: R119.1, R120.2, R121.2, U20.1
RIGHT_FILTERED: J14.4, J14.6, U13.5 (+)

Notes on the sheet:
Jumpers: 1/2: Bypass DSP 3/34 and 5/6: Connect DSP
Switch DSP and DAC In/Out
Buffer for ESP32
OPAMP Decoupling Capacitance
Low Pass Bessel
Input Gain and Buffer
