bengineer91/Preamp/kicad/Output.kicad_sch

## KiCad design kicad/Output.kicad_sch (2026-02-03)

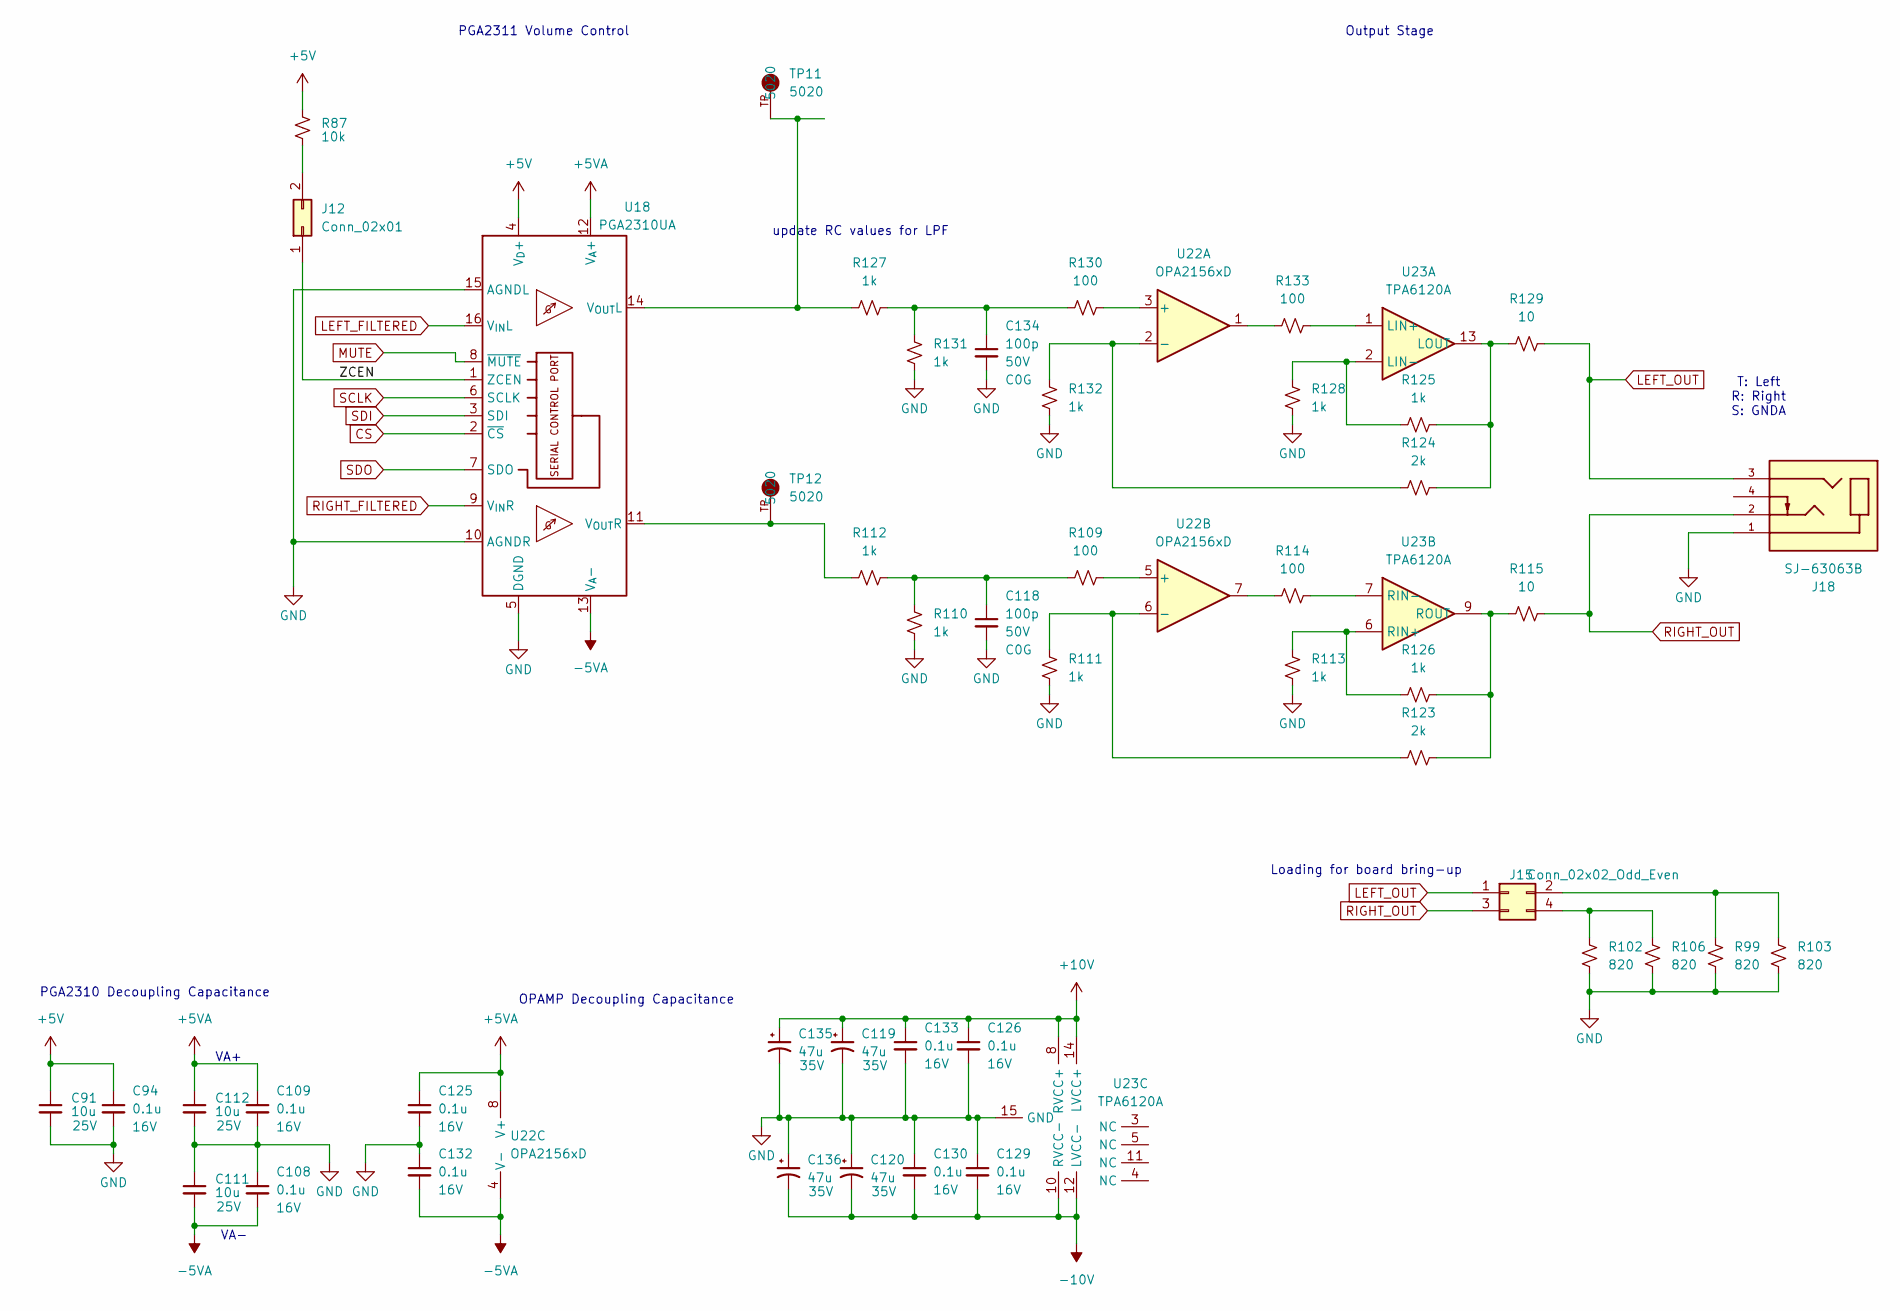
[picture p27: schematic Output.kicad_sch]

Parts:
C91, C111, C112: 10u; C_0805_2012Metric; Voltage 25V; Part Number GRM21BZ71E106KE15L
C94, C108, C109, C125, C126, C129, C130, C132, C133: 0.1u; C_0603_1608Metric; Voltage 16V; Part Number GCJ188R71C104KA01D
C118, C134: 100p; C_0603_1608Metric; Voltage 50V; Part Number GRM1885C1H101JA01D
C119, C120, C135, C136: 47u; CAP_UCD_5X5P8_NCH; Voltage 35V; Part Number UCM1V470MCL1GS
J12: Conn_02x01; PinHeader_1x02_P2.54mm_Vertical
J15: Conn_02x02_Odd_Even; PinHeader_2x02_P2.54mm_Vertical
J18: SJ-63063B; CUI_SJ-63063B; Part Number SJ-63063B
R87: 10k; R_0603_1608Metric; Part Number CRCW060310K0FKEA
R99, R102, R103, R106: 820; R_0805_2012Metric_HandSolder; Part Number CRCW0805820RFKEA
R109, R114, R130, R133: 100; R_0603_1608Metric_Pad0.98x0.95mm_HandSolder
R110, R111, R112, R113, R125, R126, R127, R128, R131, R132: 1k; R_0603_1608Metric; Part Number CRCW06031K00FKEA
R115, R129: 10; R_1206_3216Metric
R123, R124: 2k; R_0603_1608Metric
TP11, TP12: 5020; KEYSTONE_5020; PARTREV C
U18: PGA2310UA; SOIC-16W_7.5x10.3mm_P1.27mm; Part Number PGA2310UA
U22: OPA2156xD; SOIC-8_3.9x4.9mm_P1.27mm; Manufacturer_Part_Number OPA2156IDR
U23: TPA6120A; RGY0014A; Part Number TPA6120A2RGYR

Connections:
+5V: C91.1, C94.1, R87.2, U18.4 (V_{D}+)
+5VA: C109.1, C112.1, C125.1, U18.12 (V_{A}+), U22.8 (V+)
+10V: C119.1, C126.1, C133.1, C135.1, U23.8 (RVCC+), U23.14 (LVCC+)
-5VA: C108.2, C111.2, C132.2, U18.13 (V_{A}-), U22.4 (V-)
-10V: C120.2, C129.2, C130.2, C136.2, U23.10 (RVCC-), U23.12 (LVCC-)
CS: U18.2 (~CS)
GND: C91.2, C94.2, C108.1, C109.2, C111.1, C112.2, C118.2, C119.2, C120.1, C125.2, C126.2, C129.1, C130.1, C132.1, C133.2, C134.2, C135.2, C136.1, J18.1, R99.2, R102.2, R103.2, R106.2, R110.2, R111.1, R113.2, R128.2, R131.2, R132.1, U18.5 (DGND), U18.10 (AGNDR), U18.15 (AGNDL), U23.15 (GND)
LEFT_FILTERED: U18.16 (V_{IN}L)
LEFT_OUT: J15.1, J18.3, R129.1
MUTE: U18.8 (~MUTE)
unnamed: C118.1, R109.1, R110.1, R112.2
unnamed: C134.1, R127.2, R130.1, R131.1
unnamed: J12.2, R87.1
unnamed: J15.2, R99.1, R103.1
unnamed: J15.4, R102.1, R106.1
unnamed: R109.2, U22.5 (+)
unnamed: R111.2, R123.1, U22.6 (-)
unnamed: R112.1, TP12.TP, U18.11 (V_{OUT}R)
unnamed: R113.1, R126.1, U23.6 (RIN+)
unnamed: R114.1, U22.7
unnamed: R114.2, U23.7 (RIN-)
unnamed: R115.2, R123.2, R126.2, U23.9 (ROUT)
unnamed: R124.1, R132.2, U22.2 (-)
unnamed: R124.2, R125.2, R129.2, U23.13 (LOUT)
unnamed: R125.1, R128.1, U23.2 (LIN-)
unnamed: R127.1, TP11.TP, U18.14 (V_{OUT}L)
unnamed: R130.2, U22.3 (+)
unnamed: R133.1, U22.1
unnamed: R133.2, U23.1 (LIN+)
RIGHT_FILTERED: U18.9 (V_{IN}R)
RIGHT_OUT: J15.3, J18.2, R115.1
SCLK: U18.6 (SCLK)
SDI: U18.3 (SDI)
SDO: U18.7 (SDO)
ZCEN: J12.1, U18.1 (ZCEN)

Notes on the sheet:
T: Left R: Right S: GNDA
Output Stage
PGA2311 Volume Control
update RC values for LPF
OPAMP Decoupling Capacitance
Loading for board bring-up
PGA2310 Decoupling Capacitance
VA-
VA+
