bengineer91/Preamp/kicad/Power.kicad_sch

## KiCad design kicad/Power.kicad_sch (2026-02-03)

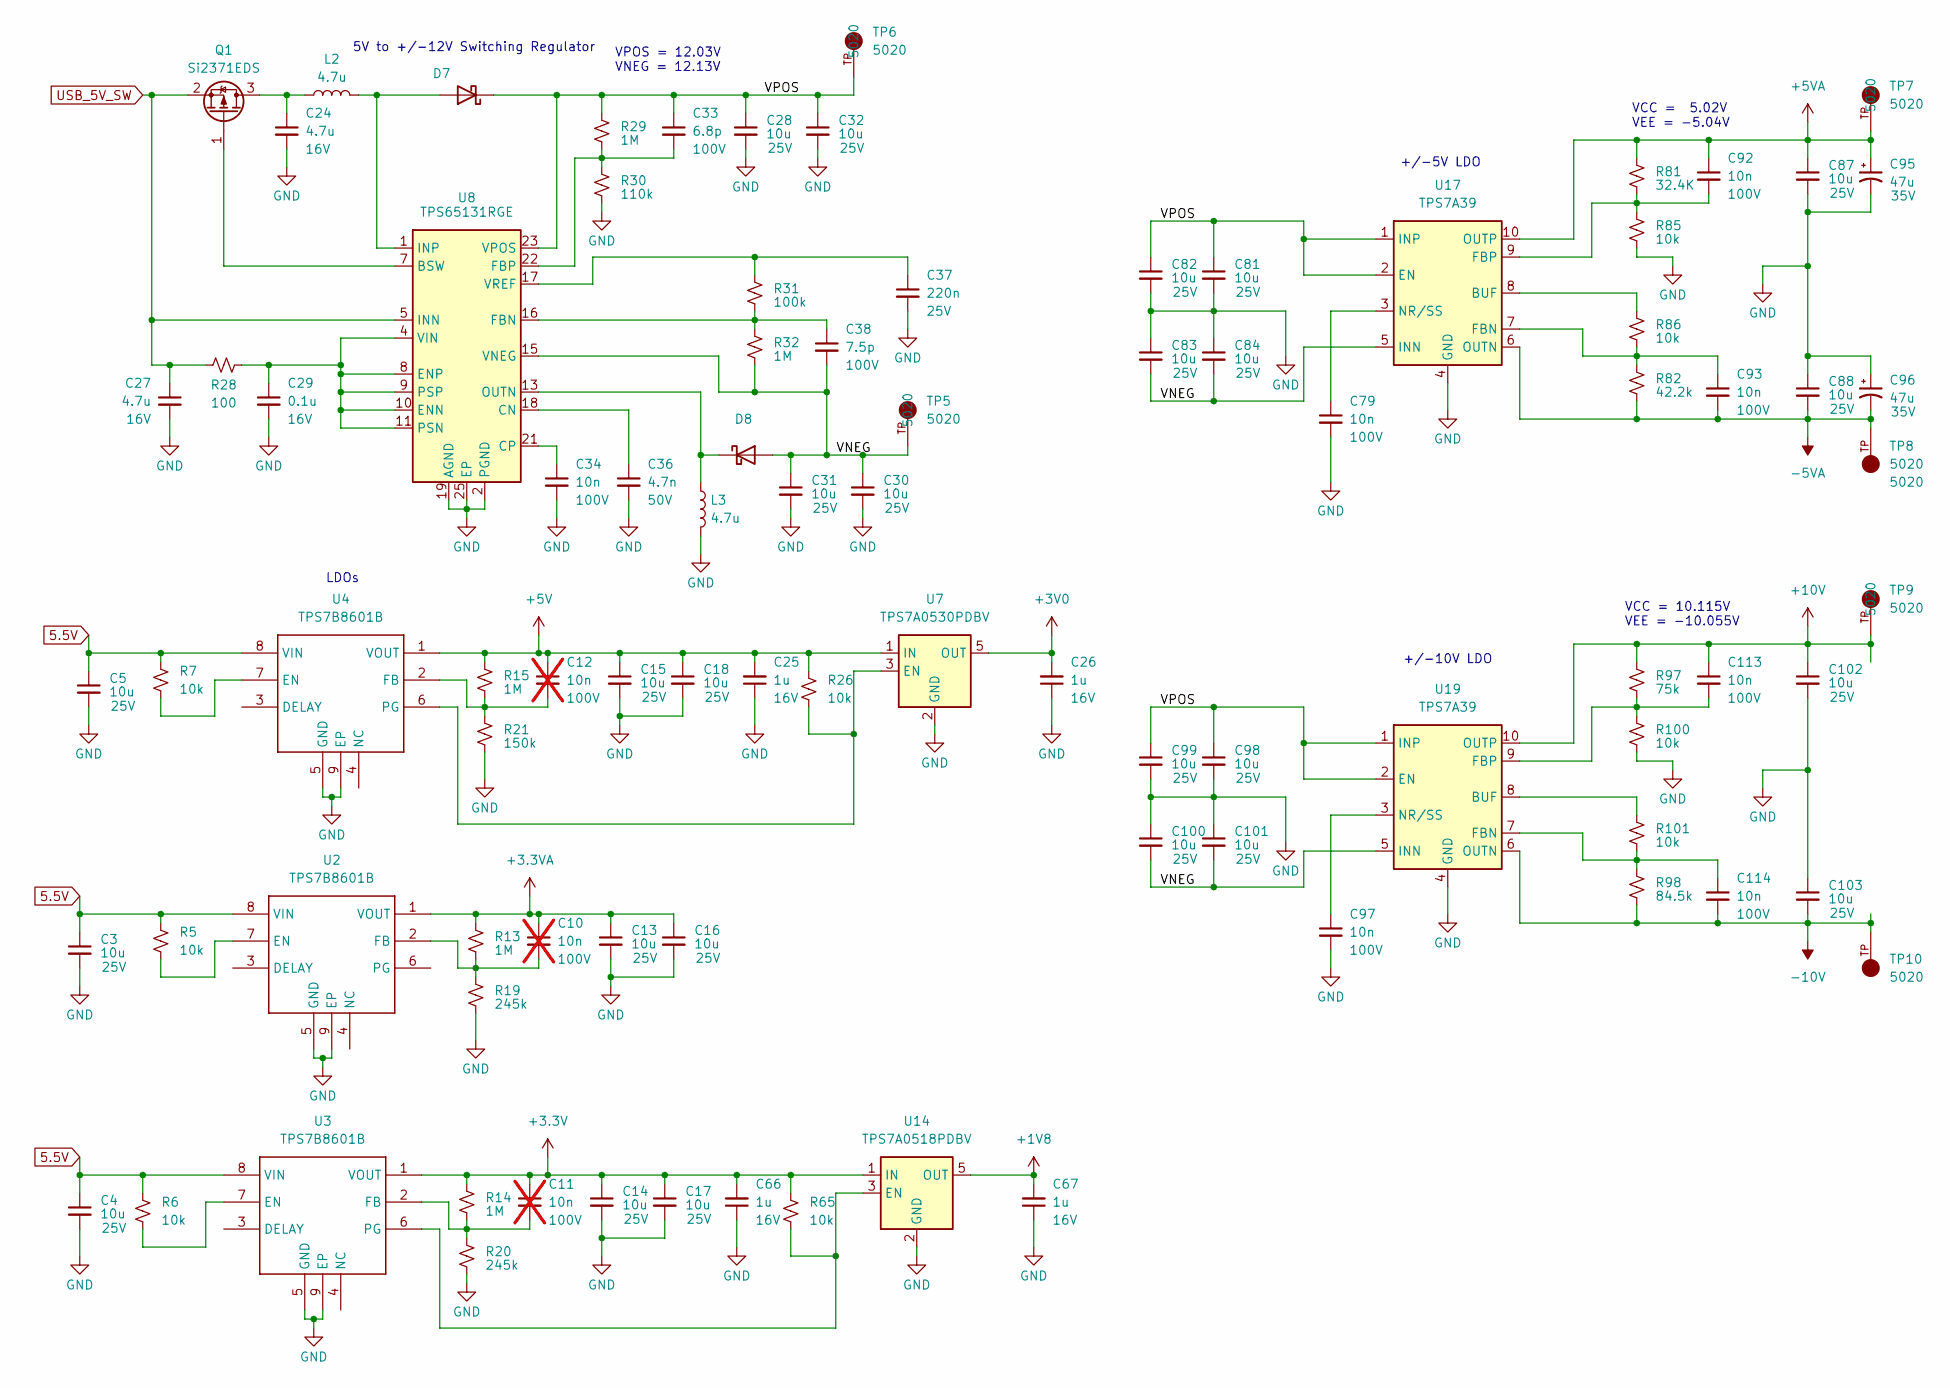
[picture p28: schematic Power.kicad_sch]

Parts:
C3, C4, C5, C13, C14, C15, C16, C17, C18, C28, C30, C31, C32, C81, C82, C83, C84, C87, C88, C98, C99, C100, C101, C102, C103: 10u; C_0805_2012Metric; Voltage 25V; Part Number GRM21BZ71E106KE15L
C10, C11, C12: 10n; C_0603_1608Metric; Voltage 100V; Part Number GCM188R72A103KA37D; not fitted
C24, C27: 4.7u; C_0805_2012Metric_Pad1.18x1.45mm_HandSolder; Voltage 16V; Part Number GRM188Z71C475KE21D
C25, C26, C66, C67: 1u; C_0805_2012Metric_HandSolder; Voltage 16V; Part Number 0805YC105KAT2A
C29: 0.1u; C_0603_1608Metric; Voltage 16V; Part Number GCJ188R71C104KA01D
C33: 6.8p; C_0603_1608Metric; Voltage 100V
C34, C79, C92, C93, C97, C113, C114: 10n; C_0603_1608Metric; Voltage 100V; Part Number GCM188R72A103KA37D
C36: 4.7n; C_0603_1608Metric; Voltage 50V; Part Number GCM188R71H472KA37J
C37: 220n; C_0603_1608Metric; Voltage 25V; Part Number GRM188R71E224KA88D
C38: 7.5p; C_0603_1608Metric; Voltage 100V
C95, C96: 47u; CAP_UCD_5X5P8_NCH; Voltage 35V; Part Number UCM1V470MCL1GS
D7, D8: D_SOD-123; Part Number MBR120
L2, L3: 4.7u; L_Wuerth_MAPI-4020; Part Number 74438357047
Q1: Si2371EDS; SOT-23; Manufacturer_Part_Number Si2371EDS
R5, R6, R7, R26, R65, R85, R86, R100, R101: 10k; R_0603_1608Metric; Part Number CRCW060310K0FKEA
R13: 1M; R_0603_1608Metric_Pad0.98x0.95mm_HandSolder; Part Number CRCW060332K4FKEA
R14: 1M; R_0603_1608Metric; Part Number CRCW080532K4FKEA
R15: 1M; R_0603_1608Metric; Part Number CRCW060332K4FKEA
R19: 245k; R_0603_1608Metric_Pad0.98x0.95mm_HandSolder; Part Number CRCW060324K5FKEA
R20: 245k; R_0603_1608Metric
R21: 150k; R_0603_1608Metric; Part Number CRCW060315K0FKEA
R28: 100; R_0603_1608Metric; Part Number CRCW0603100RFKEA
R29: 1M; R_0603_1608Metric
R30: 110k; R_0603_1608Metric
R31: 100k; R_0603_1608Metric; Part Number CRCW0603100KFKEA
R32: 1M; R_0603_1608Metric; Part Number CRCW06031M00FKEA
R81: 32.4K; R_0603_1608Metric; Part Number CRCW060332K4FKEA
R82: 42.2k; R_0603_1608Metric; Part Number CRCW060342K2FKEA
R97: 75k; R_0603_1608Metric; Part Number CRCW060375K0FKEA
R98: 84.5k; R_0603_1608Metric; Part Number CRCW060384K5FKEA
TP5, TP6, TP7, TP8, TP9, TP10: 5020; KEYSTONE_5020; PARTREV C
U2, U3, U4: TPS7B8601B; TI_SO-PowerPAD-8; Part Number TPS7B8601BQDDARQ1
U7: TPS7A0530PDBV; SOT-23-5; Manufacturer_Part_Number TPS7A0530PDBV
U8: TPS65131RGE; VQFN-24-1EP_4x4mm_P0.5mm_EP2.45x2.45mm_ThermalVias; Manufacturer_Part_Number TPS65131RGE
U14: TPS7A0518PDBV; SOT-23-5; Manufacturer_Part_Number TPS7A0518PDBV
U17, U19: TPS7A39; Texas_S-PVSON-N10; Part Number TPS7A3901DSCR

Connections:
5.5V: C3.1, C4.1, C5.1, R5.2, R6.2, R7.2, U2.8 (VIN), U3.8 (VIN), U4.8 (VIN)
+1V8: C67.2, U14.5 (OUT)
+3.3V: C11.1, C14.1, C17.1, C66.2, R14.2, R65.2, U3.1 (VOUT), U14.1 (IN)
+3.3VA: C10.1, C13.1, C16.1, R13.2, U2.1 (VOUT)
+3V0: C26.2, U7.5 (OUT)
+5V: C12.1, C15.1, C18.1, C25.2, R15.2, R26.2, U4.1 (VOUT), U7.1 (IN)
+5VA: C87.1, C92.1, C95.1, R81.2, TP7.TP, U17.10 (OUTP)
+10V: C102.1, C113.1, R97.2, TP9.TP, U19.10 (OUTP)
-5VA: C88.2, C93.2, C96.2, R82.1, TP8.TP, U17.6 (OUTN)
-10V: C103.2, C114.2, R98.1, TP10.TP, U19.6 (OUTN)
GND: C3.2, C4.2, C5.2, C13.2, C14.2, C15.2, C16.2, C17.2, C18.2, C24.2, C25.1, C26.1, C27.2, C28.2, C29.2, C30.2, C31.2, C32.2, C34.2, C36.2, C37.2, C66.1, C67.1, C79.2, C81.2, C82.2, C83.1, C84.1, C87.2, C88.1, C95.2, C96.1, C97.2, C98.2, C99.2, C100.1, C101.1, C102.2, C103.1, L3.2, R19.1, R20.1, R21.1, R30.1, R85.1, R100.1, U2.5 (GND), U2.9 (EP), U3.5 (GND), U3.9 (EP), U4.5 (GND), U4.9 (EP), U7.2 (GND), U8.2 (PGND), U8.3 (PGND), U8.19 (AGND), U8.25 (EP), U14.2 (GND), U17.4 (GND), U17.11 (GND), U19.4 (GND), U19.11 (GND)
unnamed: C10.2, R13.1, R19.2, U2.2 (FB)
unnamed: C11.2, R14.1, R20.2, U3.2 (FB)
unnamed: C12.2, R15.1, R21.2, U4.2 (FB)
unnamed: C24.1, L2.1, Q1.3 (D)
unnamed: C29.1, R28.2, U8.4 (VIN), U8.8 (ENP), U8.9 (PSP), U8.10 (ENN), U8.11 (PSN)
unnamed: C33.2, R29.1, R30.2, U8.22 (FBP)
unnamed: C34.1, U8.21 (CP)
unnamed: C36.1, U8.18 (CN)
unnamed: C37.1, R31.2, U8.17 (VREF)
unnamed: C38.1, R31.1, R32.2, U8.16 (FBN)
unnamed: C79.1, U17.3 (NR/SS)
unnamed: C92.2, R81.1, R85.2, U17.9 (FBP)
unnamed: C93.1, R82.2, R86.1, U17.7 (FBN)
unnamed: C97.1, U19.3 (NR/SS)
unnamed: C113.2, R97.1, R100.2, U19.9 (FBP)
unnamed: C114.1, R98.2, R101.1, U19.7 (FBN)
unnamed: D7.2 (A), L2.2, U8.1 (INP), U8.24 (INP)
unnamed: D8.1 (K), L3.1, U8.13 (OUTN), U8.14 (OUTN)
unnamed: Q1.1 (G), U8.7 (BSW)
unnamed: R5.1, U2.7 (EN)
unnamed: R6.1, U3.7 (EN)
unnamed: R7.1, U4.7 (EN)
unnamed: R26.1, U4.6 (PG), U7.3 (EN)
unnamed: R65.1, U3.6 (PG), U14.3 (EN)
unnamed: R86.2, U17.8 (BUF)
unnamed: R101.2, U19.8 (BUF)
USB_5V_SW: C27.1, Q1.2 (S), R28.1, U8.5 (INN), U8.6 (INN)
VNEG: C30.1, C31.1, C38.2, C83.2, C84.2, C100.2, C101.2, D8.2 (A), R32.1, TP5.TP, U8.15 (VNEG), U17.5 (INN), U19.5 (INN)
VPOS: C28.1, C32.1, C33.1, C81.1, C82.1, C98.1, C99.1, D7.1 (K), R29.2, TP6.TP, U8.23 (VPOS), U17.1 (INP), U17.2 (EN), U19.1 (INP), U19.2 (EN)

Notes on the sheet:
LDOs
5V to +/-12V Switching Regulator
VCC = 5.02V VEE = -5.04V
+/-10V LDO
+/-5V LDO
VCC = 10.115V VEE = -10.055V
VPOS = 12.03V VNEG = 12.13V
