bengineer91/Preamp/kicad/USB.kicad_sch

## KiCad design kicad/USB.kicad_sch (2026-02-03)

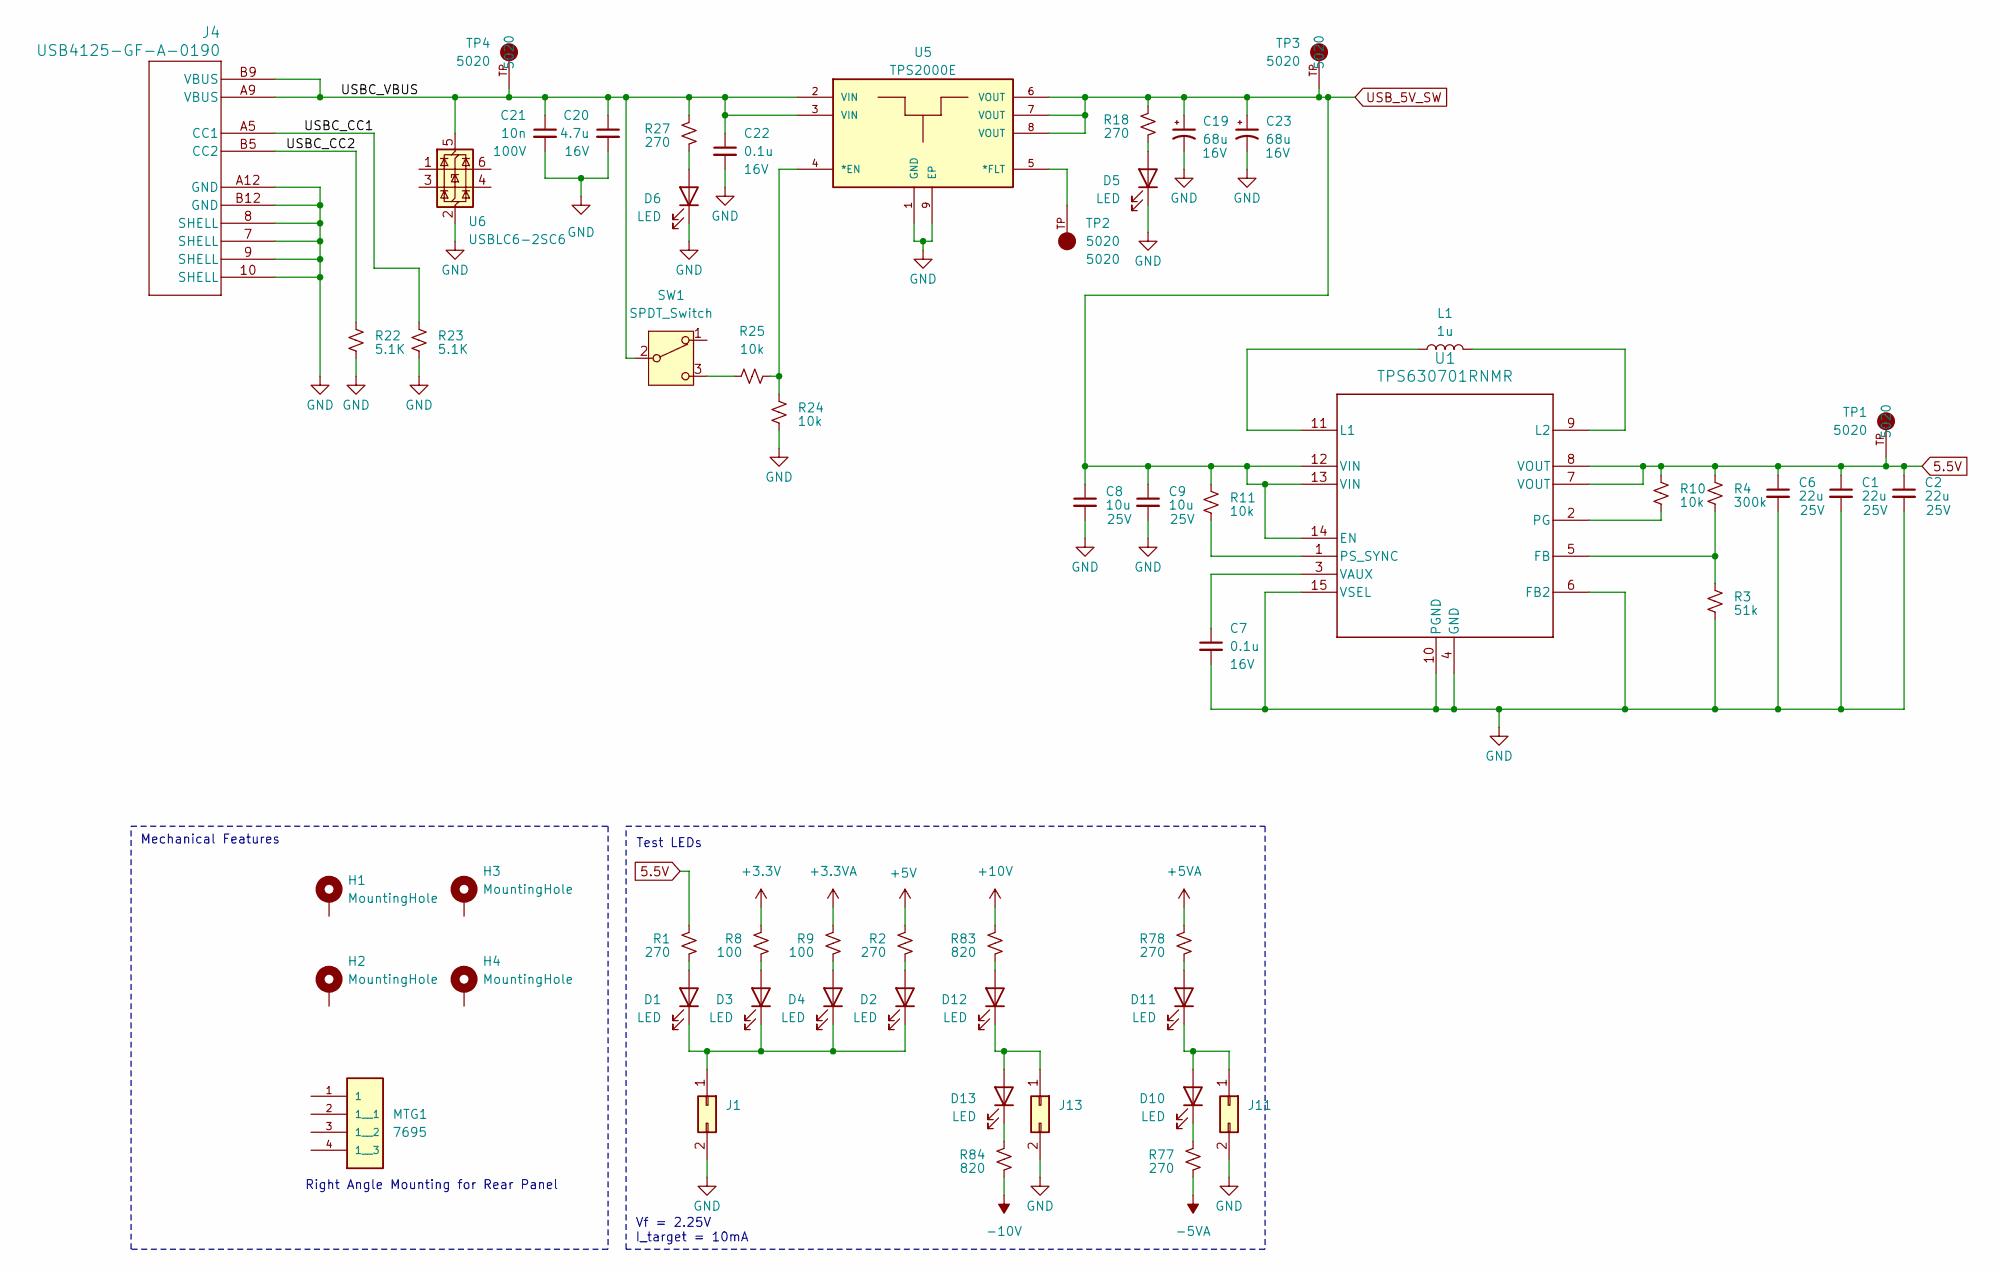
[picture p29: schematic USB.kicad_sch]

Parts:
C1, C2, C6: 22u; C_1210_3225Metric; Voltage 25V; Part Number GRM32ER71E226ME15L
C7, C22: 0.1u; C_0603_1608Metric; Voltage 16V; Part Number GCJ188R71C104KA01D
C8, C9: 10u; C_0805_2012Metric; Voltage 25V; Part Number GRM21BZ71E106KE15L
C19, C23: 68u; CP_EIA-6032-28_Kemet-C; Voltage 16V; Part Number T495C686M016ATE250
C20: 4.7u; C_0805_2012Metric_Pad1.18x1.45mm_HandSolder; Voltage 16V; Part Number GRM188Z71C475KE21D
C21: 10n; C_0603_1608Metric; Voltage 100V; Part Number GCM188R72A103KA37D
D1, D2, D3, D4, D5, D6, D10, D11, D12, D13: LED; LED_0805_2012Metric_Pad1.15x1.40mm_HandSolder; Part Number APT2012PGW
H1, H2, H3, H4: MountingHole; MountingHole_3.2mm_M3_Pad_Via
J1, J11, J13: Conn_02x01; PinHeader_1x02_P1.27mm_Vertical; Part Number FTS-102-01-L-S
J4: USB4125-GF-A-0190; CONN6_125-GF-A-0190_GCT; Part Number USB4125-GF-A-0190
L1: 1u; L_Wuerth_MAPI-2512; Part Number 74438324010
MTG1: 7695; KEYSTONE_7695; Part Number 7695
R1, R2, R18, R27, R77, R78: 270; R_0805_2012Metric_HandSolder; Part Number CRCW0805150RFKEA
R3: 51k; R_0603_1608Metric
R4: 300k; R_0603_1608Metric
R8, R9: 100; R_0805_2012Metric_HandSolder; Part Number CRCW0805150RFKEA
R10, R11, R24, R25: 10k; R_0603_1608Metric; Part Number CRCW060310K0FKEA
R22, R23: 5.1K; R_0603_1608Metric; Part Number CRCW06035K10FKEA
R83, R84: 820; R_0805_2012Metric_HandSolder; Part Number CRCW0805150RFKEA
SW1: SPDT_Switch; 100AWSP1T2B4M7RE
TP1, TP2, TP3, TP4: 5020; KEYSTONE_5020; PARTREV C
U1: TPS630701RNMR; RNM0015A; Part Number TPS630701RNMR
U5: TPS2000E; Texas_DGN0008G_VSSOP-8-1EP_3x3mm_P0.65mm_EP2x2.94mm_Mask1.8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; Part Number TPS2000EDGNR
U6: USBLC6-2SC6; SOT-23-6; Manufacturer_Part_Number USBLC6-2SC6

Connections:
5.5V: C1.1, C2.1, C6.1, R1.1, R4.1, R10.1, TP1.TP, U1.7 (VOUT), U1.8 (VOUT)
+3.3V: R8.1
+3.3VA: R9.1
+5V: R2.1
+5VA: R78.1
+10V: R83.1
-5VA: R77.2
-10V: R84.2
GND: C1.2, C2.2, C6.2, C7.2, C8.2, C9.2, C19.2, C20.2, C21.2, C22.2, C23.2, D5.1 (K), D6.1 (K), J1.2, J4.7 (SHELL), J4.8 (SHELL), J4.9 (SHELL), J4.10 (SHELL), J4.A12 (GND), J4.B12 (GND), J11.2, J13.2, R3.2, R22.2, R23.2, R24.2, U1.4 (GND), U1.6 (FB2), U1.10 (PGND), U1.15 (VSEL), U5.1 (GND), U5.9 (EP), U6.2 (GND)
unnamed: C7.1, U1.3 (VAUX)
unnamed: D1.1 (K), D2.1 (K), D3.1 (K), D4.1 (K), J1.1
unnamed: D1.2 (A), R1.2
unnamed: D2.2 (A), R2.2
unnamed: D3.2 (A), R8.2
unnamed: D4.2 (A), R9.2
unnamed: D5.2 (A), R18.2
unnamed: D6.2 (A), R27.2
unnamed: D10.1 (K), R77.1
unnamed: D10.2 (A), D11.1 (K), J11.1
unnamed: D11.2 (A), R78.2
unnamed: D12.1 (K), D13.2 (A), J13.1
unnamed: D12.2 (A), R83.2
unnamed: D13.1 (K), R84.1
unnamed: L1.1, U1.11 (L1)
unnamed: L1.2, U1.9 (L2)
unnamed: R3.1, R4.2, U1.5 (FB)
unnamed: R10.2, U1.2 (PG)
unnamed: R11.2, U1.1 (PS_SYNC)
unnamed: R24.1, R25.2, U5.4 (*EN)
unnamed: R25.1, SW1.3 (ON)
unnamed: TP2.TP, U5.5 (*FLT)
USBC_CC1: J4.A5 (CC1), R23.1
USBC_CC2: J4.B5 (CC2), R22.1
USBC_VBUS: C20.1, C21.1, C22.1, J4.A9 (VBUS), J4.B9 (VBUS), R27.1, SW1.2 (COM), TP4.TP, U5.2 (VIN), U5.3 (VIN), U6.5 (VBUS)
USB_5V_SW: C8.1, C9.1, C19.1, C23.1, R11.1, R18.1, TP3.TP, U1.12 (VIN), U1.13 (VIN), U1.14 (EN), U5.6 (VOUT), U5.7 (VOUT), U5.8 (VOUT)

Notes on the sheet:
Mechanical Features
Vf = 2.25V I_target = 10mA
Test LEDs
Right Angle Mounting for Rear Panel
